savchuk-sergey/homelab_modular_tower/revisions/mk0.9.3/review_package/REVIEW_REQUIREMENTS_CHECKLIST.md

# mk0.9.3 Review Package Requirements Checklist

This checklist records whether evidence files exist. It does not approve the engineering design.

- Exports copied: `True`
- Assembly STEP present: `True`
- Analysis CSV count: `5`
- Manifest document count: `4`
- Renders included: `True`
- Drawings included: `True`

## CSV files

- `revisions/mk0.9.3/analysis/part_dimensions.csv`
- `revisions/mk0.9.3/analysis/printability_check.csv`
- `revisions/mk0.9.3/analysis/plastic_estimate.csv`
- `revisions/mk0.9.3/analysis/stl_quality.csv`
- `revisions/mk0.9.3/analysis/duplicate_geometry_check.csv`

## Manifest files

- `revisions/mk0.9.3/PRINTABLE_PARTS.md`
- `revisions/mk0.9.3/NON_PRINTABLE_PARTS.md`
- `revisions/mk0.9.3/PLACEHOLDERS.md`
- `revisions/mk0.9.3/REVIEW_GEOMETRY.md`
