savchuk-sergey/homelab_modular_tower/reviews/mk0.7.3/kimi_swarm_action_plan.md

# Action Plan for Codex — Homelab Modular Tower mk0.7.3

**Generated by:** Kimi Agents Swarm Rough Print Review  
**Date:** 2025-01-09  
**Revision:** mk0.7.3  
**Verdict:** GO FOR COUPON TEST PRINT ONLY

---

## Immediate Fixes (Before Coupon Print)

These fixes resolve BLOCKER and HIGH findings that prevent any meaningful physical assembly.

### Fix 1: Left Panel Orientation — `cad/assembly/tower_assembly.py`
**Finding:** ASM-001 (HIGH) — Left panel ribs and mounting bosses face outward.  
**Root cause:** Both left and right panels use the same `SIDE_PANEL_ASSEMBLY_ROTATION_DEG = 90.0`.  
**Fix:** Change the left panel rotation to `-90.0` (or `270.0`) so the +Y_local face (ribs/bosses) maps to +X_global, which is inward for the left panel at X=-96.5.

```python
# In tower_assembly.py, _add_side_panels():
rotations = {
    "left": -90.0,   # or 270.0
    "right": 90.0,
}
for side, (x_position, panel_factories) in factories.items():
    for index, factory in enumerate(panel_factories):
        assembly.add(
            factory(),
            name=f"{side}_side_panel_{label}",
            loc=cq.Location(
                cq.Vector(x_position, 0, side_panels.side_panel_tile_center_z(index)),
                cq.Vector(0, 0, 1),
                rotations[side],
            ),
        )
```

**Validation:** After fix, re-render `left.png` and `right.png`. Both should show smooth exteriors and ribbed interiors.

---

### Fix 2: Split-Joint Tab Overlap — `cad/parts/service_spine.py`
**Finding:** MA-003 (BLOCKER) — Both lower and upper segments have tabs at the same Z=0 location, causing physical collision.  
**Root cause:** `_split_section()` adds a tab to both lower and upper segments unconditionally.  
**Fix:** Add the tab only to the lower segment, and add a matching slot/recess to the upper segment.

```python
# In _split_section():
if section == "lower":
    tab = cq.Workplane("XY").box(...).translate((0, tab_y, tab_z))
    segment = segment.union(tab)
    segment = segment.faces(">Y").workplane(...).pushPoints(...).hole(M3_CLEARANCE)
elif section == "upper":
    # Add a matching slot/recess instead of a tab
    slot = cq.Workplane("XY").box(...).translate((0, tab_y, tab_z))
    segment = segment.cut(slot)
    # Optionally add screw holes if needed for the upper segment
```

**Validation:** After fix, run the pipeline and check that `rear_service_spine_lower` and `rear_service_spine_upper` no longer overlap in the assembly STEP export.

---

### Fix 3: Filter Retainer Clips — `cad/parts/cooling.py`
**Finding:** MA-004 (BLOCKER) — Corner clips at Y=±61 are detached from the 8 mm deep retainer body.  
**Root cause:** `clip_offset = 61` places clips 57 mm outside the body. No connecting geometry exists.  
**Fix:** Either (a) extend the retainer body depth to reach the clips, or (b) redesign the retention mechanism.

Option A (extend body):
```python
# Increase retainer depth or add ribs that connect clips to body:
connector_ribs = cq.Workplane("XY").box(BOTTOM_FILTER_RETAINER_WIDTH, clip_offset - BOTTOM_FILTER_RETAINER_DEPTH/2, BOTTOM_FILTER_RETAINER_HEIGHT)
retainer = retainer.union(connector_ribs)
```

Option B (redesign as sliding rail clips):
Replace the corner clips with small hooks that slide onto the filter frame rails.

**Validation:** After fix, the clips must be physically connected to the retainer body in the STL export. Check `stl_quality.csv` for manifold status.

---

### Fix 4: Increase Rail End Mount Engagement — `cad/parts/rails.py` or `cad/assembly/tower_assembly.py`
**Finding:** MA-002 (HIGH) — Only 3.5 mm of the 287.5 mm rail engages the mount slot.  
**Fix Option A:** Increase the slot depth in `create_rail_end_mount()`.
```python
rail_slot = cq.Workplane("XY").box(
    METAL_RAIL_WIDTH + METAL_RAIL_FRAME_CLEARANCE,
    METAL_RAIL_THICKNESS + METAL_RAIL_FRAME_CLEARANCE,
    RAIL_END_MOUNT_HEIGHT + 8.0,  # Increase from FILLET_RADIUS to +8.0
)
```

**Fix Option B:** Move the mount so the rail starts deeper in the slot.
```python
# In tower_assembly.py:
# Bottom mount: place at z = METAL_RAIL_HEIGHT/2 - (METAL_RAIL_HEIGHT - TOWER_HEIGHT + FRAME_THICKNESS) ...
# Simpler: calculate so that rail bottom enters the slot center.
```

**Validation:** After fix, the rail should engage at least 8–10 mm of the slot. Verify with a section view in the assembly.

---

### Fix 5: Add Frame Hole for Rail End Mount — `cad/parts/frame.py`
**Finding:** MA-007 (HIGH) — Rail end mount has an M3 hole with no mating target in the frame or rail.  
**Fix:** Add an M3 clearance hole to the frame at each rail position, aligned with the mount's >Y face hole.

```python
# In frame.py, after rail cutouts:
for x, y in guide_rail_positions():
    frame = frame.faces(">Z").workplane().pushPoints([(x, y)]).hole(M3_CLEARANCE)
    # Or add a dedicated mount hole offset from the rail cutout
```

**Validation:** Verify that the mount hole and frame hole are collinear in the assembly.

---

### Fix 6: Reduce Central Bottom Fan Frame Thickness — `cad/parts/feet.py` or `cad/config.py`
**Finding:** PE-001 (HIGH) — 16 mm thick, 326 g. Overbuilt for a mockup.  
**Fix:** Add a mockup parameter and reduce thickness.

```python
# In config.py, add:
MOCKUP_BASE_THICKNESS = 8.0  # mm, for rough mockup only

# In feet.py, use MOCKUP_BASE_THICKNESS instead of BASE_STABILITY_THICKNESS
# for the central_bottom_fan_frame if a mockup flag is set.
```

**Validation:** Re-export and verify the frame still has sufficient rigidity for hand-assembly.

---

## Short-Term Improvements (Before Full Mockup Print)

### Improvement 7: Add Mockup Thickness Parameters — `cad/config.py`
**Finding:** PE-002, PE-003, PE-004, PE-005 (MEDIUM) — Multiple subsystems are overbuilt for mockup.  
**Action:** Add optional `MOCKUP_*` parameters to enable quick config-driven mass reduction without altering production geometry.

```python
# In config.py:
MOCKUP_BASE_THICKNESS = 6.0
MOCKUP_CENTRAL_FRAME_THICKNESS = 8.0
MOCKUP_TRAY_BASE = 2.0
MOCKUP_TRAY_WALL = 2.0
MOCKUP_SHEAR_RIB_HEIGHT = 2.0
MOCKUP_SPINE_DEPTH = 20.0
MOCKUP_WING_THICKNESS = 6.0
```

Use these parameters in part functions when a mockup mode is enabled (e.g., via an environment variable or a config flag).

---

### Improvement 8: Generate Fastener BOM
**Finding:** RAP-007, RAP-008 (MEDIUM) — M5 nuts/washers and M3 screws/inserts are not inventoried.  
**Action:** Write a Python script that walks the assembly and counts:
- M5 nut seats (8x corner blocks × 2 faces + 4 rods × 2 ends = ~16+)
- M5 washer seats (same count)
- M3 clearance holes (panels, rails, ledges, mounts, spine, trays)
- M3 heat-set insert bosses (trays, panels, spine tabs)

Output a text file `reviews/mk0.7.3/fastener_bom.md`.

---

### Improvement 9: Write Rough Assembly Sequence
**Finding:** RAP-004 (HIGH) — No assembly instructions exist.  
**Action:** Produce a numbered step-by-step guide:

1. **Base Assembly** — Bolt together central_bottom_fan_frame, left/right extensions, front/rear wings.
2. **Rod Stack** — Insert M5 rods through bottom frame, add washers and nuts.
3. **Corner Blocks** — Slide bottom corner blocks onto rods, add washers and nuts.
4. **Guide Rails** — Insert metal guide rails into frame cutouts.
5. **Rail End Mounts** — Attach mounts at top and bottom of rails.
6. **Tray Support Ledges** — Attach ledges at module Z positions.
7. **Tray Stack** — Insert module trays from bottom to top.
8. **Rear Service Spine** — Bolt lower and upper sections together, attach to frame.
9. **Power Bus** — Attach lower and upper power bus panels, attach to spine.
10. **Side Panels** — Attach mount rails, then screw panels to rails.
11. **Fans** — Insert bottom fan cartridge, attach top/bottom grilles.
12. **Feet** — Insert TPU feet into sockets.

Include warnings about:
- Left panel orientation (must be rotated -90°)
- M5 rod cap is non-structural
- Split-joint tabs need careful alignment

---

### Improvement 10: Reduce Bottom Fan Grille Thickness — `cad/parts/cooling.py`
**Finding:** PE-009 (LOW) — Bottom grille is 7 mm thick; config specifies `FAN_GRILLE_THICKNESS=4.0`.  
**Action:** Change `bottom_fan_grille` to use `FAN_GRILLE_THICKNESS=4.0` consistently, or add a mockup parameter.

```python
# In cooling.py:
# Replace hardcoded 7 mm features with FAN_GRILLE_THICKNESS
```

---

## Validation Steps (After Fixes)

### Step 11: Re-run Revision Pipeline
After all CAD fixes, execute:
```bash
conda run -n cadquery python scripts/run_revision_pipeline.py --revision mk0.7.3
```
Verify:
- `printability_check.csv` still shows no axis-aligned overflow.
- `stl_quality.csv` still shows all printable parts as watertight/manifold.
- `plastic_estimate.csv` shows reduced mass if mockup parameters are used.

### Step 12: Print and Validate All 8 Coupons
From Section 10 of the review report:

1. **Split-joint tab coupon** — Verify tab/slot fit and M3 screw clearance.
2. **Rail end mount + metal rail coupon** — Verify 8–10 mm slot engagement and slide fit.
3. **Tray support ledge + rail + tray coupon** — Verify 1.0 mm clearance is correct after shrinkage.
4. **Side panel mount rail + panel coupon** — Verify screw fit, boss strength, and panel stiffness.
5. **Filter retainer + frame + filter coupon** — Verify clips hold filter under vibration.
6. **TPU foot + PETG socket coupon** — Verify insertion force and screw retention.
7. **Large thin flat test tile (50 × 50 × 3 mm)** — Verify brim effectiveness and corner lift.
8. **Grille test tile (50 × 50 × 4 mm section)** — Verify support-free flatness and bar adhesion.

### Step 13: Re-run This Review
After fixes and coupon validation, re-run the Kimi Agents Swarm review to confirm:
- All BLOCKERs are resolved.
- No new geometry bugs were introduced.
- The verdict can be upgraded to GO FOR ROUGH MOCKUP PRINT.

---

## Priority Summary

| Priority | Fix / Action | Effort | Impact |
|---|---|---|---|
| **P0** | Fix left panel orientation (Fix 1) | 1 line | HIGH — enables proper panel mounting |
| **P0** | Fix split-joint tab overlap (Fix 2) | ~10 lines | BLOCKER — enables spine assembly |
| **P0** | Fix filter retainer clips (Fix 3) | ~10 lines | BLOCKER — enables filter function |
| **P1** | Increase rail end mount engagement (Fix 4) | ~2 lines | HIGH — prevents rail wobble |
| **P1** | Add frame hole for rail mount (Fix 5) | ~5 lines | HIGH — gives mount a screw target |
| **P1** | Add mockup thickness parameters (Improvement 7) | ~10 lines | HIGH — saves 700–1000 g plastic |
| **P2** | Generate fastener BOM (Improvement 8) | Script | MEDIUM — enables hardware purchase |
| **P2** | Write assembly sequence (Improvement 9) | Document | HIGH — prevents misassembly |
| **P2** | Reduce central frame thickness (Fix 6) | ~3 lines | HIGH — saves ~100–130 g |
| **P3** | Reduce bottom grille thickness (Improvement 10) | ~2 lines | LOW — saves ~40 g, fixes inconsistency |

---

*End of action plan.*
