savchuk-sergey/homelab_modular_tower/reviews/mk0.7.3/kimi_swarm_unknowns.md

# Unknowns and Deferred Items — Homelab Modular Tower mk0.7.3

**Generated by:** Kimi Agents Swarm Rough Print Review  
**Date:** 2025-01-09  
**Revision:** mk0.7.3

---

## Unknowns (Insufficient Evidence in Current Review)

These items could not be fully evaluated due to missing evidence, incomplete code visibility, or the need for physical testing.

### UNK-001: Internal Component Intersections
**Status:** UNCERTAIN  
**Reference:** `cad/assembly/tower_assembly.py` (full assembly not fully dissected)  
**Question:** Do the inward-facing ribs on the right panel intersect with the Mini PC tray, rear service spine, or other internal components?  
**Why it matters:** The right panel ribs extend to X≈+85. The Mini PC tray is at X≈±86, Y≈−4 to +90. The spine is at Y≈+80. Depending on exact geometry, ribs may collide with tray edges or spine tabs.  
**What is needed:** A full assembly Boolean intersection check in CadQuery, or internal cross-section renders (e.g., X=+85 plane cut).  
**Evidence rule:** NEEDS TEST — requires CadQuery collision detection or physical test print.

### UNK-002: Mini PC Airflow Duct Internal Geometry
**Status:** UNCERTAIN  
**Reference:** `cad/parts/cooling.py` lines 137–155; `cad/assembly/tower_assembly.py`  
**Question:** Does the duct have internal baffles or overhangs that would require supports when printed upright?  
**Why it matters:** The duct is 88 × 134 × 62 mm with 2 mm walls. If it is an open U-channel, it prints support-free upright. If it has internal bridges or overhangs > 45°, supports are needed.  
**What is needed:** A small cross-section render or a test print of the duct base.  
**Evidence rule:** NEEDS TEST — requires slicer preview or physical test print.

### UNK-003: Side Panel Middle Section Printability
**Status:** UNCERTAIN  
**Reference:** `part_dimensions.csv` (`left_side_panel_middle`: 176 × 5.2 × 100.9 mm); `printability_check.csv`  
**Question:** Can the 5.2 mm thick middle panel be printed on edge (176 × 5.2 mm footprint, Z=100.9 mm) without excessive wobble or detachment?  
**Why it matters:** The middle panel is only 5.2 mm thick. Printing it on edge creates a very narrow wall on the bed. PETG may wobble or detach due to the small contact area.  
**What is needed:** A test print of the middle panel on edge with a wide brim.  
**Evidence rule:** NEEDS TEST — requires physical test print.

### UNK-004: Actual Metal Guide Rail Tolerance
**Status:** UNCERTAIN  
**Reference:** `cad/parts/rails.py`; `config.py` (`METAL_RAIL_FRAME_CLEARANCE=1.0`)  
**Question:** Is 1.0 mm clearance sufficient for real metal rail tolerance + PETG print shrinkage?  
**Why it matters:** The rail end mount slot is 11 × 4 mm for a 10 × 3 mm rail. After PETG shrinkage (~0.3–0.5 %), the slot may be too tight. If the rail has manufacturing tolerance (±0.2 mm), the fit may be too loose or too tight.  
**What is needed:** Source actual metal rails and print one rail end mount and one tray support ledge for fit testing.  
**Evidence rule:** NEEDS TEST — requires physical test with real hardware.

### UNK-005: TPU Foot Compression and Fit
**Status:** UNCERTAIN  
**Reference:** `cad/parts/feet.py`; `config.py` (`FOOT_SOCKET_CLEARANCE=0.6`, `FOOT_SCREW_DIAMETER=5.3`)  
**Question:** Will the TPU foot press-fit into the PETG socket with 0.6 mm clearance, or will it be too loose/tight?  
**Why it matters:** TPU compresses under load. 0.6 mm clearance may be too tight for insertion or too loose under the tower's weight. The 5.3 mm screw hole may not provide sufficient retention in TPU.  
**What is needed:** Print one foot socket (PETG) and one foot (TPU) and test insertion force and retention.  
**Evidence rule:** NEEDS TEST — requires physical test print.

### UNK-006: Bottom Filter Retainer Clip Strength After Print
**Status:** UNCERTAIN  
**Reference:** `cad/parts/cooling.py` lines 113–134; `stl_quality.csv`  
**Question:** Even if the clips are fixed to be geometrically attached, will they survive print removal and repeated flexing?  
**Why it matters:** The retainer clips are small (16 × 16 mm base) and only 4 mm tall. They must flex to snap over the filter frame. PETG may be too brittle for repeated snap-fit use, or the clips may break during removal from the build plate.  
**What is needed:** Print the fixed retainer and test clip retention with a real filter sheet.  
**Evidence rule:** NEEDS TEST — requires physical test print.

### UNK-007: M5 Rod Nut/Washer Stack Geometry
**Status:** UNCERTAIN  
**Reference:** `cad/parts/frame.py` lines 10–30; `cad/parts/corner_blocks.py` lines 17–20; `config.py`  
**Question:** Does the M5 nut seat + washer seat + rod end geometry allow the rod to be fully tensioned without the nut bottoming out on the frame or corner block?  
**Why it matters:** The rod extra thread allowance is 18 mm. The top frame has a nut seat (4.2 mm deep) and a washer seat (1.8 mm deep). The bottom frame has a washer seat (1.8 mm) and a nut seat (4.2 mm). The corner blocks add 28 mm height. The total stack may consume more than the 18 mm allowance if the rod is not cut to exact length.  
**What is needed:** A stack-height calculation and a physical test with actual M5 rods, nuts, and washers.  
**Evidence rule:** NEEDS TEST — requires physical assembly test.

### UNK-008: Side Panel Mount Rail Boss Strength
**Status:** UNCERTAIN  
**Reference:** `cad/parts/side_panels.py` lines 100–113; `config.py` (`INSERT_BOSS_DIAMETER=7.2`, `HEAT_SET_INSERT_M3_DIAMETER=5.2`)  
**Question:** Will the 7.2 mm diameter M3 insert boss withstand panel installation torque without stripping?  
**Why it matters:** The mount rail is 8 mm wide. The panel boss is 7.2 mm diameter. The screw must pass through the rail hole (3.4 mm) and into the panel boss insert. If the boss wall is too thin (7.2 mm OD − 5.2 mm insert = 2.0 mm wall / 2 = 1.0 mm per side), it may crack under torque.  
**What is needed:** Print one mount rail and one panel section, install a heat-set insert, and torque-test with an M3 screw.  
**Evidence rule:** NEEDS TEST — requires physical test print.

---

## Deferred to mk1.0 (Explicitly Out of Scope)

These items are intentionally deferred to the next major revision per project documentation and user instructions.

| Item | Deferred Reason | Source |
|---|---|---|
| Real Mini PC PCB/chassis dimensions, port locations, cooler height, 19 V input connector | Placeholder envelope only | `README.md` (Measurements Needed For v2); `KNOWN_ISSUES.md` |
| Real MikroTik hAP ax2 bare board dimensions, Ethernet jack position, DC input position, antenna keep-out | Placeholder envelope only | `README.md`; `KNOWN_ISSUES.md` |
| Real Raspberry Pi standoff pattern and exact connector clearance | Placeholder envelope only | `README.md` |
| DC UPS board, BMS, fuse block, terminal block, DC-DC converter footprints | Placeholder envelope only | `README.md` |
| Real connector footprints (XT30, JST-VH, Molex MicroFit, USB-C panel/cable) | Placeholder connector cutouts only | `README.md`; `KNOWN_ISSUES.md` |
| Exact LiFePO4 pack dimensions and safe retention method | Placeholder envelope only | `README.md` |
| Final Mini PC airflow duct validation against actual device intake/exhaust | Placeholder duct geometry | `KNOWN_ISSUES.md` |
| Final cable routing and wire harness engineering | Rough service envelope only | `KNOWN_ISSUES.md` |
| Thermal validation (CFD, smoke test, physical temperature measurement) | Not a mockup requirement | `KNOWN_ISSUES.md`; `REVISION.md` |
| Full production BOM and electrical safety review | mk0.7.3 is rough mockup only | `REVISION.md` |
| Final stability/tipping analysis with real component masses and CG | Rough stability envelope exists | `KNOWN_ISSUES.md`; user instruction |
| Metal guide rail material selection and stiffness validation | Non-printable reference only | `README.md` |
| Torsion brace hardware selection and physical testing | Mount provisions exist, no hardware specified | `config.py` (`TORSION_BRACE_MOUNT_ENABLED=True`) |
| Final power bus design, fuse values, DC current sizing | Placeholder power bus only | `KNOWN_ISSUES.md` |
| Final UPS/battery package and containment | Placeholder envelope only | `KNOWN_ISSUES.md` |
| Final side-panel shear-transfer architecture (mount rails are rough mockup only) | mk0.7.3 explicitly uses rough rails | `KNOWN_ISSUES.md` |
| Real SSD/SSD expansion dimensions and mounting | Placeholder envelopes only | `README.md` |
| Production cable management (cable ties, strain relief, bend radius) | Rough cable envelope only | `KNOWN_ISSUES.md` |

---

## Recommendations for Closing Unknowns

1. **Physical coupon testing is the only way to resolve UNK-001 through UNK-008.** The CSV and CAD evidence are sufficient to identify risks but insufficient to confirm fit, strength, or tolerance.
2. **After mk0.7.3 is stabilized, the mk1.0 revision should focus on:**
   - Measuring all real hardware and replacing placeholders with exact dimensions.
   - Finalizing the power bus, connector, and UPS geometry.
   - Running thermal validation (smoke test or simple temperature logging).
   - Performing a full stability analysis with measured masses.
   - Selecting and validating the metal guide rail material and dimensions.
   - Integrating the torsion brace if structural testing shows it is needed.

---

*End of unknowns and deferred items.*
