savchuk-sergey/homelab_modular_tower/reviews/mk0.7.1/agent_outputs/06_power_cable_management.md

# Power and Cable Management Review

**Reviewer:** Power and Cable Management Reviewer (Agent)  
**Revision:** mk0.7.1  
**Date:** 2026-06-27  
**Scope:** Power bus panel, power bus cover, strain relief, connector zones, rear service spine cable routing, cable exit alignment, DC UPS integration, mains isolation, fuse protection, fan cable routing.

---

## Executive Summary

The mk0.7.1 power system and cable management design is **conceptually sound** but **not physically viable** in its current state. The power bus panel and cover remain structural placeholders that will not survive real assembly. The rear service spine has insufficient cable capacity for the declared device count. Connector zones lack the clearance required for real panel-mount connectors. Strain relief is undersized. The DC UPS placeholder volume is optimistic. Most critically, there is no defined cable path for the bottom fan, and the 220 V external PSU is not physically integrated.

**The only change in mk0.7.1** is the power bus cover screw hole alignment: holes are now at `±POWER_BUS_PAD_SCREW_OFFSET_X` (±7 mm), matching the panel pad holes. This fix is correct but cosmetic; it does not address the fundamental rigidity, capacity, or routing blockers.

**Overall grade: NEEDS SIGNIFICANT REDESIGN before mk0.8.**

| Finding | Grade | Urgency |
|---|---|---|
| Power bus panel rigidity | **CONFIRMED** — inadequate | High |
| Power bus cover stiffness | **CONFIRMED** — inadequate | High |
| Strain relief sizing | **LIKELY** — too small | Medium |
| Connector zone / cover gap | **CONFIRMED** — collision | High |
| Spine cable routing capacity | **CONFIRMED** — insufficient | High |
| Cable exit alignment | **LIKELY** — too tight | Medium |
| DC UPS integration | **NEEDS TEST** | Medium |
| Mains voltage isolation | **CONFIRMED** — not modeled | Medium |
| Fuse and protection | **CONFIRMED** — placeholder only | Medium |
| Fan cable routing | **CONFIRMED** — undefined | High |

---

## Power Bus Panel Design

### Geometry
- Panel dimensions: **34 mm wide × 7.5 mm thick (max) × 275.5 mm tall** (from `config.py`: `POWER_BUS_WIDTH = 34.0`, `POWER_BUS_THICKNESS = 3.0`, `POWER_BUS_HEIGHT = 275.5`).
- Base material thickness: **3.0 mm**.
- Four rail pads: 22 mm wide × 4 mm deep × 22 mm tall, located at Z offsets `+70`, `+25`, `-20`, `-65` relative to panel center.
- M3 holes for rail pads at `±7 mm` from center, cut on the back face (`<Y`).
- No explicit mounting holes to the rear spine or frame.

### Structural Analysis
The panel is a tall, thin strip of PETG with a height-to-thickness ratio of **275.5 / 3.0 = 91.8:1**. Even with the 4 mm deep rail pads, the effective thickness is only 7.5 mm locally, and the pads are only 22 mm tall — they do not create a continuous beam. A 275 mm tall PETG panel with 3 mm base thickness will bow visibly under its own weight (estimated panel mass ≈ 30–40 g, but the real concern is cable insertion forces). When an operator plugs in an XT30 connector, the insertion force (typically 10–20 N) will flex the panel like a leaf spring. The panel has no vertical ribs, no frame tabs, and no lateral support except the cover guard rails.

The rail pads are only screwed with M3 holes, but there is no information about what they screw into. The `POWER_BUS_PAD_Y = -3.5` places the pads on the back face, but the rear spine channel wall is at Y = 65 (world), while the panel back face is at Y = 68.5. The pads do not contact the spine; they float in the channel gap.

### Evidence
- `config.py:531–533`: `POWER_BUS_THICKNESS = 3.0`, `POWER_BUS_HEIGHT = TOWER_HEIGHT - 46.0 = 275.5`.
- `service_spine.py:8–41`: The panel is a simple `box(34, 3, 275.5)` with pads and holes. No ribs, no frame mounts, no spine attachment.
- `part_dimensions.csv:83`: `power_bus_panel` bounding box is `34.0 × 7.5 × 275.5` mm.

### Grade: **CONFIRMED** — The panel is not rigid enough for real connectors.

---

## Power Bus Cover Adequacy

### Geometry
- Cover dimensions: **46 mm wide × 5.0 mm thick (max) × 265.5 mm tall** (from `config.py`: `POWER_BUS_COVER_WIDTH = 46.0`, `POWER_BUS_COVER_THICKNESS = 2.4`, `POWER_BUS_COVER_HEIGHT = 265.5`).
- Base material thickness: **2.4 mm**.
- Guard rails: 3 mm wide × 5 mm deep, running the full height on both sides.

### Structural Analysis
A 2.4 mm thick PETG panel 265 mm tall has a height-to-thickness ratio of **265.5 / 2.4 = 110.6:1**. This is even more flexible than the panel. The guard rails add some stiffness, but they are only 3 mm wide and 5 mm deep — they act as edge stiffeners, not as structural ribs. The cover will act as a leaf spring. During assembly or when cables are pressed against it, it will bow inward toward the panel. With only ~0.2 mm gap between the cover guard rails and the panel back face, even slight deflection will cause contact and potential shorting if wires are routed in the gap.

The cover is now mounted with M3 screws at the correct `±7 mm` X offsets, matching the panel rail pads. The code uses `for _, z in cfg.POWER_BUS_RAIL_LABELS: cover.hole(M3_CLEARANCE)` at the rail Z positions, with holes at `(-7, z)` and `(7, z)`. This means there are still only **4 screw pairs** (8 holes) along the entire 265 mm height, spaced at rail positions (70, 25, -20, -65). For a 265 mm tall cover, 4 screw pairs are insufficient to prevent bowing between screws. The span between screws is ~45–90 mm, and a 2.4 mm PETG panel will sag between mounts.

### Fix Verification
The mk0.7.1 change in `service_spine.py:57–60` correctly sets the cover holes to `±POWER_BUS_PAD_SCREW_OFFSET_X` (7.0 mm), matching the panel M3 holes. This is a valid bug fix, but it does not change the structural assessment.

### Evidence
- `config.py:551–554`: `POWER_BUS_COVER_THICKNESS = 2.4`, `POWER_BUS_COVER_HEIGHT = 265.5`.
- `service_spine.py:44–61`: Cover is a `box(46, 2.4, 265.5)` with guard rails and 8 M3 holes at ±7 mm.
- `part_dimensions.csv:82`: `power_bus_cover` bounding box is `46.0 × 5.0 × 265.5` mm.

### Grade: **CONFIRMED** — The cover will flex significantly and is insufficiently supported. The hole alignment fix is correct but insufficient for structural viability.

---

## Strain Relief Analysis

### Geometry
- Strain relief clamps: **24 mm wide × 8 mm tall × 6 mm deep** (`POWER_BUS_STRAIN_RELIEF_WIDTH = 24.0`, `POWER_BUS_STRAIN_RELIEF_HEIGHT = 8.0`, `POWER_BUS_STRAIN_RELIEF_DEPTH = 6.0`).
- Four clamps at Z positions: `-112`, `-48`, `+48`, `+112` relative to panel center.
- Each clamp has a cable tie slot: `slot2D(12, 4, 0)` — i.e., **4 mm wide × 12 mm tall** slot.

### Analysis
An XT30 connector with 14 AWG silicone wire has a wire bundle diameter of approximately **4.5–5.5 mm**. The clamp height is only **8 mm**, which means the clamp can barely accommodate one cable in the vertical direction. The clamp depth is **6 mm**, which is the thickness of the clamp body in the Y direction. The cable tie slot is only **4 mm wide** — standard cable ties are 2.5–4.8 mm wide, so this just fits a small tie, but the slot is cut through the entire clamp, meaning the cable is only constrained by the cable tie, not by a proper saddle or gland.

For USB-C cables with thicker molded strain relief (6–8 mm diameter), the clamp is too small entirely. For Ethernet cables (Cat 6, ~6 mm diameter), the clamp is also undersized. The clamps are essentially small PETG blocks with a through-slot — they provide no clamping force without a cable tie, and the cable tie slot is too small to use a proper locking tie.

Furthermore, the clamps are placed only at the four connector zone heights. If a module uses a cable that is longer or routed differently, there is no intermediate strain relief.

### Evidence
- `config.py:556–559`: Strain relief dimensions and Z positions.
- `service_spine.py:29–40`: Clamp geometry and cable tie slot.
- Render image: The clamps are small protrusions on the panel sides.

### Grade: **LIKELY** — Strain relief is inadequate for typical XT30 and USB-C cables with thick insulation.

---

## Connector Zone Sizing

### Geometry
Connector zones are through-cut rectangular cutouts on the panel back face (`<Y`):

| Zone | Dimensions (W×H) | Z Position (rel. center) | Rail | Rail Z (rel. center) |
|---|---|---|---|---|
| XT30 (19V) | 24 × 14 mm | +112 mm | 19V | +70 mm |
| MicroFit (12V) | 20 × 10 mm | +48 mm | 12V | +25 mm |
| USB-C (5V) | 18 × 8 mm | -48 mm | 5V | -20 mm |
| Cable tie | 24 × 10 mm | -112 mm | GND | -65 mm |

### Critical Gap Problem
The connector zones are cut through the 3.0 mm panel with `cutBlind(-5.0)`, making them through-holes. The connectors would be mounted on the panel front face (`>Y`, Y = 71.5 world). However, the **cover is only 2.2–3.2 mm behind the panel back face** (Y = 68.5 for panel back, Y = 65.8–68.3 for cover assembly). This leaves **0.2–2.7 mm** of clearance behind the panel.

A panel-mount XT30 connector has a body that extends **10–15 mm** behind the mounting flange. A MicroFit panel mount extends **8–12 mm** behind. A USB-C panel mount extends **6–10 mm**. All of these would **collide with the cover or guard rails**.

### Vertical Alignment Problem
The connector zones are not aligned with the rail pads. For example, the XT30 zone is at Z = +112 mm, but the 19V rail pad is at Z = +70 mm. The vertical offset is 42 mm. This means the connector is 42 mm away from the rail it serves. The wires would need to run internally 42 mm, but the panel is only 3 mm thick — there is no internal wiring channel. The actual wiring would need to snake around the panel edges, which are only 5 mm from the panel side (panel is 34 mm wide, rail pads are 22 mm wide, leaving 6 mm margins).

### Horizontal Alignment Problem
The module cable exits are 66 mm wide, but the power bus panel is only 34 mm wide. The connector zones are centered at X = 0. However, some devices have their power jacks offset:
- Mini PC power window is at `X = -54.0` relative to tray center (`config.py:306`).
- The power bus panel is at X = 0 world, so the Mini PC power connector at X = -54 would need to reach 54 mm horizontally to the centered connector zone. But the power bus panel is only 17 mm wide from center to edge (34 mm total). The connector at X = -54 is outside the panel entirely.
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
