savchuk-sergey/homelab_modular_tower/revisions/mk0.9.3/NON_PRINTABLE_PARTS.md

# Non-Printable Reference Parts

Revision: `mk0.9.3`

This manifest lists generated export artifacts. CadQuery source remains the source of truth.

No artifacts found for this category.
