savchuk-sergey/homelab_modular_tower/revisions/mk0.9.1/BOM.md

# mk0.9.1 Bill of Materials (BOM)

## Printed parts (PETG)

| Part | Target weight | Qty | Notes |
|---|---|-----|---|
| Base module | 180–260 g | 1 | Frame + fan mount + grill + filter slot + foot mounts |
| RPi/SSD carriage | 80–130 g | 1 | Open-frame, 4 POM-C shoes |
| Mini PC placeholder carriage | 100–180 g | 1 | Open-frame, 6 POM-C shoes |
| Roof module | 150–230 g | 1 | Frame + fan mount + grill + shroud |
| M5 rod caps | 5–10 g | 4 | Protective end caps |
| Rail end clips | 2–4 g | 4 | Retain U-channel rail ends |
| Small brackets / stops | 10–20 g | — | Miscellaneous |
| **Total PETG target** | **750–900 g** | | |
| **Total PETG hard limit** | **≤ 1100 g** | | |

## Printed parts (TPU)

| Part | Target weight | Qty | Notes |
|---|---|-----|---|
| TPU feet | 8–12 g | 4 | Replaceable, M5 through-hole |
| **Total TPU target** | **≤ 50 g** | | |

## Hardware

| Item | Qty | Notes |
|---|-----|---|
| M5 threaded rod × 4 | 4 | Length = tower height + ~18 mm thread allowance |
| M5 nut | 8 | 4 bottom, 4 top |
| M5 washer | 8 | Optional, spreads load on frame |
| M3 × 12 mm screw | ~20 | Module interfaces, rail clips, shoe clamps |
| M3 × 16 mm screw | 4 | Front carriage locks |
| M3 heat-set insert | ~20 | Brass, ~5 mm OD, 4 mm length |
| M3 × 4 mm screw | 8 | 120 mm fan mounting (4 per fan) |

## Commercial / non-printed parts

| Item | Qty | Notes |
|---|-----|---|
| Aluminum U-channel 15 × 10 × 10 × 2 mm | 2 × 145 mm + 2 × 155 mm | Side rails for carriages; cut from 1800 mm stock |
| POM-C rod Ø8 mm | 1 × 500 mm | Cut into 12 mm shoe blanks (4 + 6 + spares) |
| 120 mm × 120 mm × 25 mm fan | 2 | Bottom intake, top exhaust |
| Dust filter material | 1 sheet | Cut to fit filter slot |
| Top guard mesh | 1 sheet | Optional coarse filter for exhaust |

## Electronics (placeholder)

| Item | Qty | Notes |
|---|-----|---|
| Raspberry Pi 3B | 1 | Mounted on carriage standoffs |
| External SSD | 1 | 2.5" or M.2 enclosure |
| Mini PC placeholder | 1 | Real device measured in mk1.0 |
