savchuk-sergey/homelab_modular_tower/revisions/mk0.9.2/NON_PRINTABLE_PARTS.md

# Non-Printable Reference Parts

Revision: `mk0.9.2`

This manifest lists generated export artifacts. CadQuery source remains the source of truth.

## aluminum_u_channel_rail_placeholder

- Category: `non_printable`
- STEP: `exports/mk0.9.2/non_printable/metal_reference/aluminum_u_channel_rail_placeholder.step`
- STL: `exports/mk0.9.2/non_printable/metal_reference/aluminum_u_channel_rail_placeholder.stl`

## m5_threaded_rod

- Category: `non_printable`
- STEP: `exports/mk0.9.2/non_printable/metal_reference/m5_threaded_rod.step`
- STL: `exports/mk0.9.2/non_printable/metal_reference/m5_threaded_rod.stl`
