savchuk-sergey/homelab_modular_tower/revisions/mk0.9.2/PRINTABLE_PARTS.md

# Printable Parts

Revision: `mk0.9.2`

This manifest lists generated export artifacts. CadQuery source remains the source of truth.

## base_module

- Category: `printable`
- STEP: `exports/mk0.9.2/printable/plastic/base_module.step`
- STL: `exports/mk0.9.2/printable/plastic/base_module.stl`

## bottom_grill

- Category: `printable`
- STEP: `exports/mk0.9.2/printable/plastic/bottom_grill.step`
- STL: `exports/mk0.9.2/printable/plastic/bottom_grill.stl`

## dust_filter_slot

- Category: `printable`
- STEP: `exports/mk0.9.2/printable/plastic/dust_filter_slot.step`
- STL: `exports/mk0.9.2/printable/plastic/dust_filter_slot.stl`

## foot_mounts

- Category: `printable`
- STEP: `exports/mk0.9.2/printable/plastic/foot_mounts.step`
- STL: `exports/mk0.9.2/printable/plastic/foot_mounts.stl`

## m5_threaded_rod_cap

- Category: `printable`
- STEP: `exports/mk0.9.2/printable/plastic/m5_threaded_rod_cap.step`
- STL: `exports/mk0.9.2/printable/plastic/m5_threaded_rod_cap.stl`

## mini_pc_placeholder_carriage

- Category: `printable`
- STEP: `exports/mk0.9.2/printable/plastic/mini_pc_placeholder_carriage.step`
- STL: `exports/mk0.9.2/printable/plastic/mini_pc_placeholder_carriage.stl`

## mini_pc_placeholder_module

- Category: `printable`
- STEP: `exports/mk0.9.2/printable/plastic/mini_pc_placeholder_module.step`
- STL: `exports/mk0.9.2/printable/plastic/mini_pc_placeholder_module.stl`

## rail_end_clip

- Category: `printable`
- STEP: `exports/mk0.9.2/printable/plastic/rail_end_clip.step`
- STL: `exports/mk0.9.2/printable/plastic/rail_end_clip.stl`

## roof_module

- Category: `printable`
- STEP: `exports/mk0.9.2/printable/plastic/roof_module.step`
- STL: `exports/mk0.9.2/printable/plastic/roof_module.stl`

## rpi_ssd_carriage

- Category: `printable`
- STEP: `exports/mk0.9.2/printable/plastic/rpi_ssd_carriage.step`
- STL: `exports/mk0.9.2/printable/plastic/rpi_ssd_carriage.stl`

## rpi_ssd_module

- Category: `printable`
- STEP: `exports/mk0.9.2/printable/plastic/rpi_ssd_module.step`
- STL: `exports/mk0.9.2/printable/plastic/rpi_ssd_module.stl`

## top_filter_slot

- Category: `printable`
- STEP: `exports/mk0.9.2/printable/plastic/top_filter_slot.step`
- STL: `exports/mk0.9.2/printable/plastic/top_filter_slot.stl`

## foot

- Category: `printable`
- STEP: `exports/mk0.9.2/printable/tpu/foot.step`
- STL: `exports/mk0.9.2/printable/tpu/foot.stl`

## tpu_foot_placeholder

- Category: `printable`
- STEP: `exports/mk0.9.2/printable/tpu/tpu_foot_placeholder.step`
- STL: `exports/mk0.9.2/printable/tpu/tpu_foot_placeholder.stl`
