savchuk-sergey/homelab_modular_tower/revisions/mk0.7.3/PRINTABLE_PARTS.md

# Printable Parts

Revision: `mk0.7.3`

This manifest lists generated export artifacts. CadQuery source remains the source of truth.

## bottom_fan_cartridge

- Category: `printable`
- STEP: `exports/mk0.7.3/printable/plastic/bottom_fan_cartridge.step`
- STL: `exports/mk0.7.3/printable/plastic/bottom_fan_cartridge.stl`

## bottom_fan_grille

- Category: `printable`
- STEP: `exports/mk0.7.3/printable/plastic/bottom_fan_grille.step`
- STL: `exports/mk0.7.3/printable/plastic/bottom_fan_grille.stl`

## bottom_filter_frame

- Category: `printable`
- STEP: `exports/mk0.7.3/printable/plastic/bottom_filter_frame.step`
- STL: `exports/mk0.7.3/printable/plastic/bottom_filter_frame.stl`

## bottom_filter_retainer

- Category: `printable`
- STEP: `exports/mk0.7.3/printable/plastic/bottom_filter_retainer.step`
- STL: `exports/mk0.7.3/printable/plastic/bottom_filter_retainer.stl`

## bottom_structural_frame

- Category: `printable`
- STEP: `exports/mk0.7.3/printable/plastic/bottom_structural_frame.step`
- STL: `exports/mk0.7.3/printable/plastic/bottom_structural_frame.stl`

## central_bottom_fan_frame

- Category: `printable`
- STEP: `exports/mk0.7.3/printable/plastic/central_bottom_fan_frame.step`
- STL: `exports/mk0.7.3/printable/plastic/central_bottom_fan_frame.stl`

## corner_block

- Category: `printable`
- STEP: `exports/mk0.7.3/printable/plastic/corner_block.step`
- STL: `exports/mk0.7.3/printable/plastic/corner_block.stl`

## external_ssd_bay

- Category: `printable`
- STEP: `exports/mk0.7.3/printable/plastic/external_ssd_bay.step`
- STL: `exports/mk0.7.3/printable/plastic/external_ssd_bay.stl`

## foot_socket

- Category: `printable`
- STEP: `exports/mk0.7.3/printable/plastic/foot_socket.step`
- STL: `exports/mk0.7.3/printable/plastic/foot_socket.stl`

## front_stability_wing

- Category: `printable`
- STEP: `exports/mk0.7.3/printable/plastic/front_stability_wing.step`
- STL: `exports/mk0.7.3/printable/plastic/front_stability_wing.stl`

## left_foot_extension

- Category: `printable`
- STEP: `exports/mk0.7.3/printable/plastic/left_foot_extension.step`
- STL: `exports/mk0.7.3/printable/plastic/left_foot_extension.stl`

## left_side_panel_lower

- Category: `printable`
- STEP: `exports/mk0.7.3/printable/plastic/left_side_panel_lower.step`
- STL: `exports/mk0.7.3/printable/plastic/left_side_panel_lower.stl`

## left_side_panel_middle

- Category: `printable`
- STEP: `exports/mk0.7.3/printable/plastic/left_side_panel_middle.step`
- STL: `exports/mk0.7.3/printable/plastic/left_side_panel_middle.stl`

## left_side_panel_upper

- Category: `printable`
- STEP: `exports/mk0.7.3/printable/plastic/left_side_panel_upper.step`
- STL: `exports/mk0.7.3/printable/plastic/left_side_panel_upper.stl`

## m5_threaded_rod_cap

- Category: `printable`
- STEP: `exports/mk0.7.3/printable/plastic/m5_threaded_rod_cap.step`
- STL: `exports/mk0.7.3/printable/plastic/m5_threaded_rod_cap.stl`

## mikrotik_tray

- Category: `printable`
- STEP: `exports/mk0.7.3/printable/plastic/mikrotik_tray.step`
- STL: `exports/mk0.7.3/printable/plastic/mikrotik_tray.stl`

## mini_pc_airflow_duct

- Category: `printable`
- STEP: `exports/mk0.7.3/printable/plastic/mini_pc_airflow_duct.step`
- STL: `exports/mk0.7.3/printable/plastic/mini_pc_airflow_duct.stl`

## mini_pc_tray

- Category: `printable`
- STEP: `exports/mk0.7.3/printable/plastic/mini_pc_tray.step`
- STL: `exports/mk0.7.3/printable/plastic/mini_pc_tray.stl`

## mini_pc_tray_stop

- Category: `printable`
- STEP: `exports/mk0.7.3/printable/plastic/mini_pc_tray_stop.step`
- STL: `exports/mk0.7.3/printable/plastic/mini_pc_tray_stop.stl`

## power_bus_cover_lower

- Category: `printable`
- STEP: `exports/mk0.7.3/printable/plastic/power_bus_cover_lower.step`
- STL: `exports/mk0.7.3/printable/plastic/power_bus_cover_lower.stl`

## power_bus_cover_upper

- Category: `printable`
- STEP: `exports/mk0.7.3/printable/plastic/power_bus_cover_upper.step`
- STL: `exports/mk0.7.3/printable/plastic/power_bus_cover_upper.stl`

## power_bus_panel_lower

- Category: `printable`
- STEP: `exports/mk0.7.3/printable/plastic/power_bus_panel_lower.step`
- STL: `exports/mk0.7.3/printable/plastic/power_bus_panel_lower.stl`

## power_bus_panel_upper

- Category: `printable`
- STEP: `exports/mk0.7.3/printable/plastic/power_bus_panel_upper.step`
- STL: `exports/mk0.7.3/printable/plastic/power_bus_panel_upper.stl`

## rail_end_mount

- Category: `printable`
- STEP: `exports/mk0.7.3/printable/plastic/rail_end_mount.step`
- STL: `exports/mk0.7.3/printable/plastic/rail_end_mount.stl`

## raspberry_pi_tray

- Category: `printable`
- STEP: `exports/mk0.7.3/printable/plastic/raspberry_pi_tray.step`
- STL: `exports/mk0.7.3/printable/plastic/raspberry_pi_tray.stl`

## rear_service_spine_cover_lower

- Category: `printable`
- STEP: `exports/mk0.7.3/printable/plastic/rear_service_spine_cover_lower.step`
- STL: `exports/mk0.7.3/printable/plastic/rear_service_spine_cover_lower.stl`

## rear_service_spine_cover_upper

- Category: `printable`
- STEP: `exports/mk0.7.3/printable/plastic/rear_service_spine_cover_upper.step`
- STL: `exports/mk0.7.3/printable/plastic/rear_service_spine_cover_upper.stl`

## rear_service_spine_lower

- Category: `printable`
- STEP: `exports/mk0.7.3/printable/plastic/rear_service_spine_lower.step`
- STL: `exports/mk0.7.3/printable/plastic/rear_service_spine_lower.stl`

## rear_service_spine_upper

- Category: `printable`
- STEP: `exports/mk0.7.3/printable/plastic/rear_service_spine_upper.step`
- STL: `exports/mk0.7.3/printable/plastic/rear_service_spine_upper.stl`

## rear_stability_wing

- Category: `printable`
- STEP: `exports/mk0.7.3/printable/plastic/rear_stability_wing.step`
- STL: `exports/mk0.7.3/printable/plastic/rear_stability_wing.stl`

## right_foot_extension

- Category: `printable`
- STEP: `exports/mk0.7.3/printable/plastic/right_foot_extension.step`
- STL: `exports/mk0.7.3/printable/plastic/right_foot_extension.stl`

## right_side_panel_lower

- Category: `printable`
- STEP: `exports/mk0.7.3/printable/plastic/right_side_panel_lower.step`
- STL: `exports/mk0.7.3/printable/plastic/right_side_panel_lower.stl`

## right_side_panel_middle

- Category: `printable`
- STEP: `exports/mk0.7.3/printable/plastic/right_side_panel_middle.step`
- STL: `exports/mk0.7.3/printable/plastic/right_side_panel_middle.stl`

## right_side_panel_upper

- Category: `printable`
- STEP: `exports/mk0.7.3/printable/plastic/right_side_panel_upper.step`
- STL: `exports/mk0.7.3/printable/plastic/right_side_panel_upper.stl`

## side_panel_mount_rail_lower

- Category: `printable`
- STEP: `exports/mk0.7.3/printable/plastic/side_panel_mount_rail_lower.step`
- STL: `exports/mk0.7.3/printable/plastic/side_panel_mount_rail_lower.stl`

## side_panel_mount_rail_middle

- Category: `printable`
- STEP: `exports/mk0.7.3/printable/plastic/side_panel_mount_rail_middle.step`
- STL: `exports/mk0.7.3/printable/plastic/side_panel_mount_rail_middle.stl`

## side_panel_mount_rail_upper

- Category: `printable`
- STEP: `exports/mk0.7.3/printable/plastic/side_panel_mount_rail_upper.step`
- STL: `exports/mk0.7.3/printable/plastic/side_panel_mount_rail_upper.stl`

## ssd_expansion_tray

- Category: `printable`
- STEP: `exports/mk0.7.3/printable/plastic/ssd_expansion_tray.step`
- STL: `exports/mk0.7.3/printable/plastic/ssd_expansion_tray.stl`

## top_fan_grille

- Category: `printable`
- STEP: `exports/mk0.7.3/printable/plastic/top_fan_grille.step`
- STL: `exports/mk0.7.3/printable/plastic/top_fan_grille.stl`

## top_structural_frame

- Category: `printable`
- STEP: `exports/mk0.7.3/printable/plastic/top_structural_frame.step`
- STL: `exports/mk0.7.3/printable/plastic/top_structural_frame.stl`

## tray_support_ledge

- Category: `printable`
- STEP: `exports/mk0.7.3/printable/plastic/tray_support_ledge.step`
- STL: `exports/mk0.7.3/printable/plastic/tray_support_ledge.stl`

## ups_power_tray

- Category: `printable`
- STEP: `exports/mk0.7.3/printable/plastic/ups_power_tray.step`
- STL: `exports/mk0.7.3/printable/plastic/ups_power_tray.stl`

## foot

- Category: `printable`
- STEP: `exports/mk0.7.3/printable/tpu/foot.step`
- STL: `exports/mk0.7.3/printable/tpu/foot.stl`
