savchuk-sergey/homelab_modular_tower/revisions/mk0.7/review_package/manifests/NON_PRINTABLE_PARTS.md

# Non-Printable Reference Parts

Revision: `mk0.7`

This manifest lists generated export artifacts. CadQuery source remains the source of truth.

## m5_threaded_rod

- Category: `non_printable`
- STEP: `exports/mk0.7/non_printable/metal_reference/m5_threaded_rod.step`
- STL: `exports/mk0.7/non_printable/metal_reference/m5_threaded_rod.stl`

## metal_guide_rail

- Category: `non_printable`
- STEP: `exports/mk0.7/non_printable/metal_reference/metal_guide_rail.step`
- STL: `exports/mk0.7/non_printable/metal_reference/metal_guide_rail.stl`
