savchuk-sergey/homelab_modular_tower/revisions/mk0.7/review_package/exports/review/airflow_path_review.step

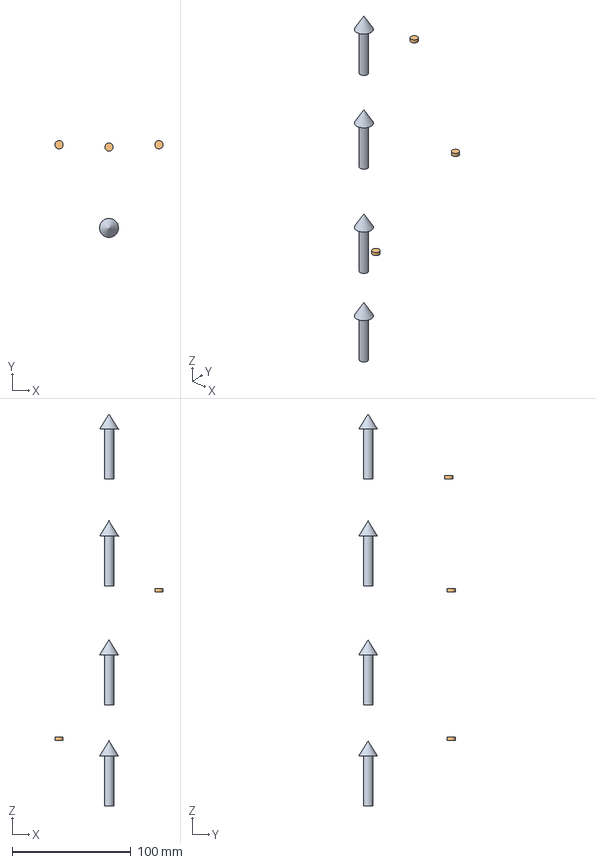
[picture p15: CAD file, 2026-06-27, last stored version]
revisions/mk0.7/review_package/exports/review/airflow_path_review.step
91.0 x 81.5 x 329.8 mm
