savchuk-sergey/homelab_modular_tower/revisions/mk0.7/review_package/exports/placeholders/devices/ssd_expansion_placeholder.step

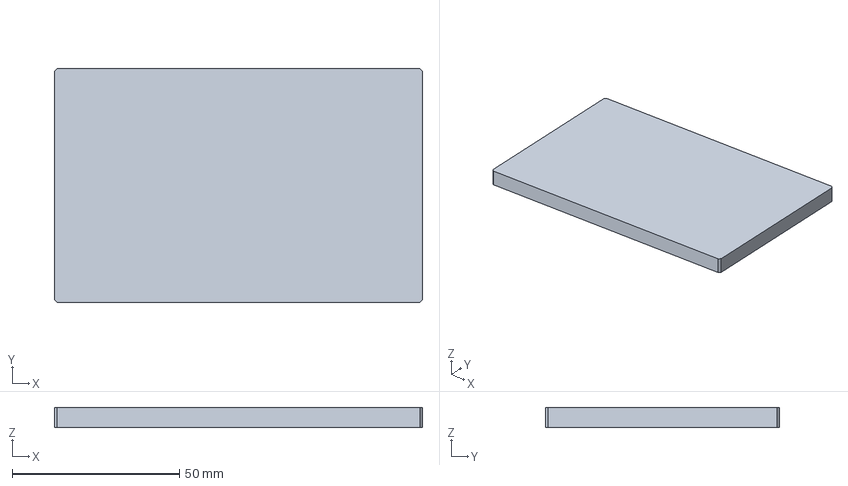
[picture p16: CAD file, 2026-06-27, last stored version]
revisions/mk0.7/review_package/exports/placeholders/devices/ssd_expansion_placeholder.step
110.0 x 70.0 x 6.00 mm
