savchuk-sergey/homelab_modular_tower/revisions/mk0.7/review_package/exports/review/printability_layout_review.step

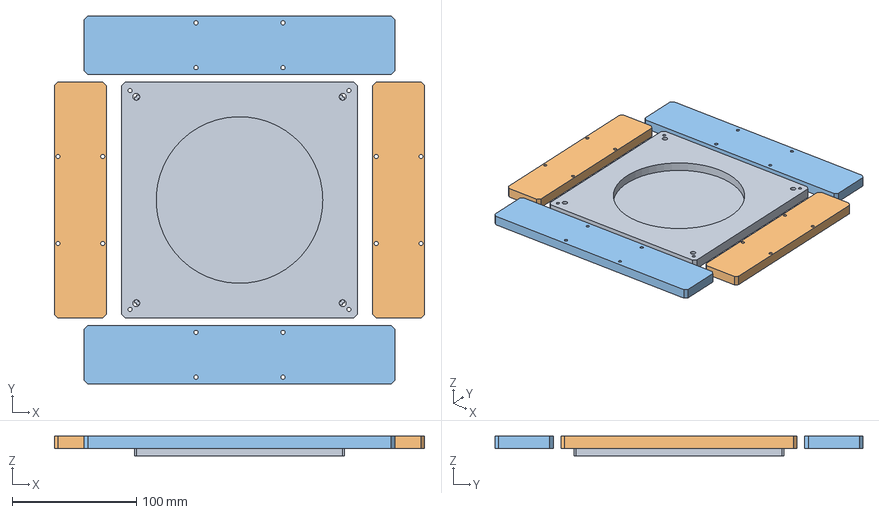
[picture p18: CAD file, 2026-06-27, last stored version]
revisions/mk0.7/review_package/exports/review/printability_layout_review.step
298.0 x 296.0 x 16.0 mm
