savchuk-sergey/homelab_modular_tower/revisions/mk0.7/review_package/exports/placeholders/devices/ssd_placeholder.step

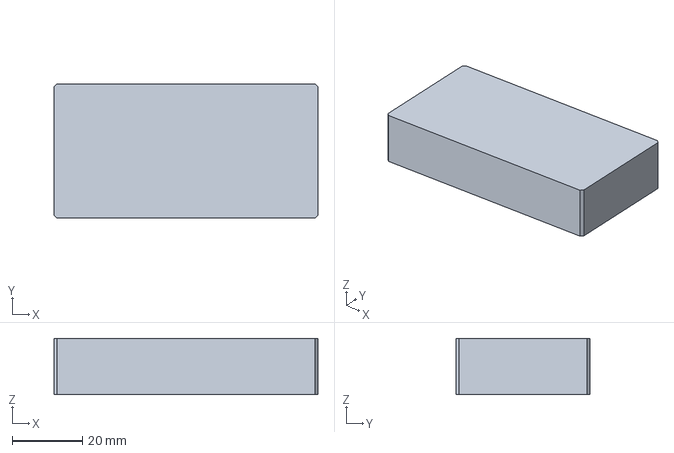
[picture p19: CAD file, 2026-06-27, last stored version]
revisions/mk0.7/review_package/exports/placeholders/devices/ssd_placeholder.step
75.0 x 38.0 x 16.0 mm
