savchuk-sergey/homelab_modular_tower/revisions/mk0.7/review_package/exports/printable/plastic/central_bottom_fan_frame.step

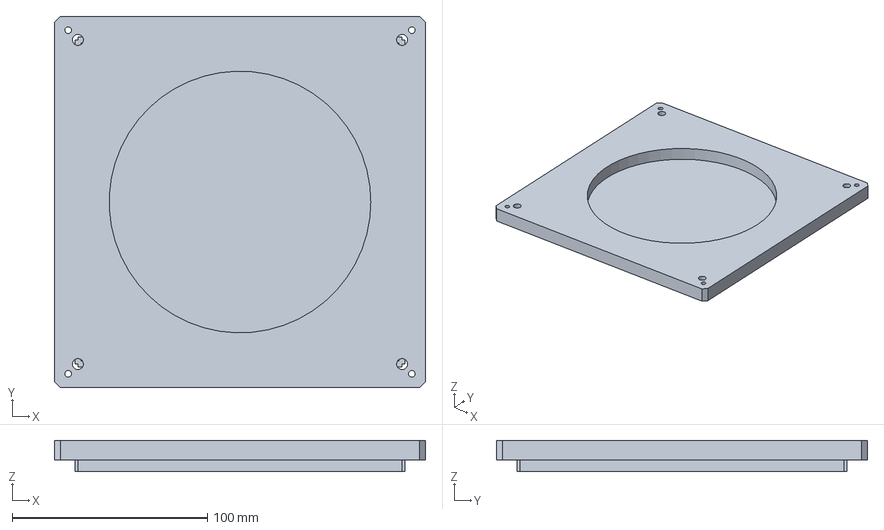
[picture p20: CAD file, 2026-06-27, last stored version]
revisions/mk0.7/review_package/exports/printable/plastic/central_bottom_fan_frame.step
190.0 x 190.0 x 16.0 mm
