savchuk-sergey/homelab_modular_tower/revisions/mk0.7/review_package/exports/review/bottom_intake_open_area_review.step

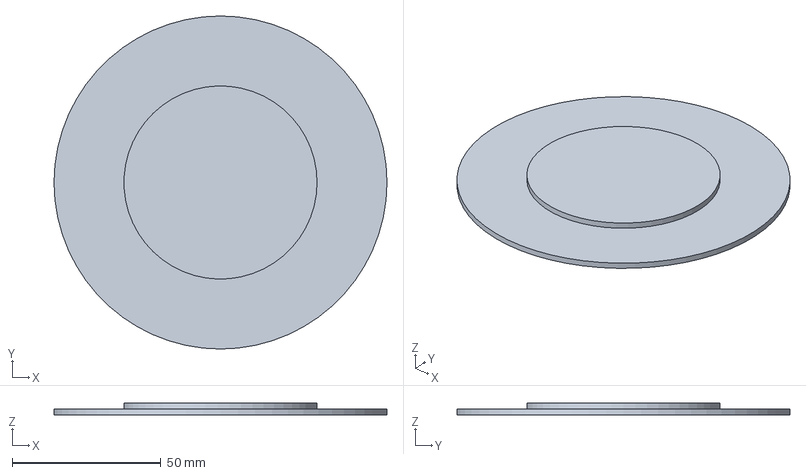
[picture p21: CAD file, 2026-06-27, last stored version]
revisions/mk0.7/review_package/exports/review/bottom_intake_open_area_review.step
112.0 x 112.0 x 4.00 mm
