savchuk-sergey/homelab_modular_tower/exports/mk0.1/step/top_fan_panel.step

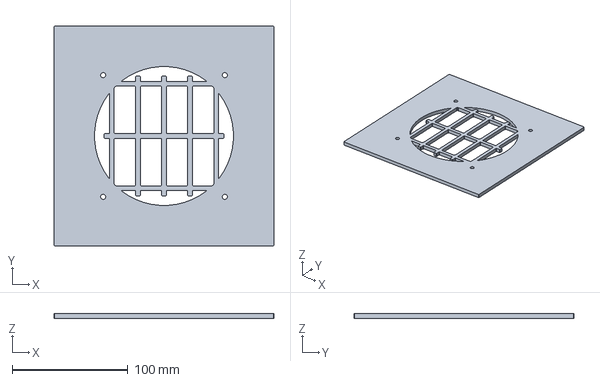
[picture p22: CAD file, 2026-06-27, last stored version]
exports/mk0.1/step/top_fan_panel.step
190.0 x 190.0 x 4.00 mm
