savchuk-sergey/homelab_modular_tower/revisions/mk0.7/review_package/exports/printable/plastic/bottom_filter_frame.step

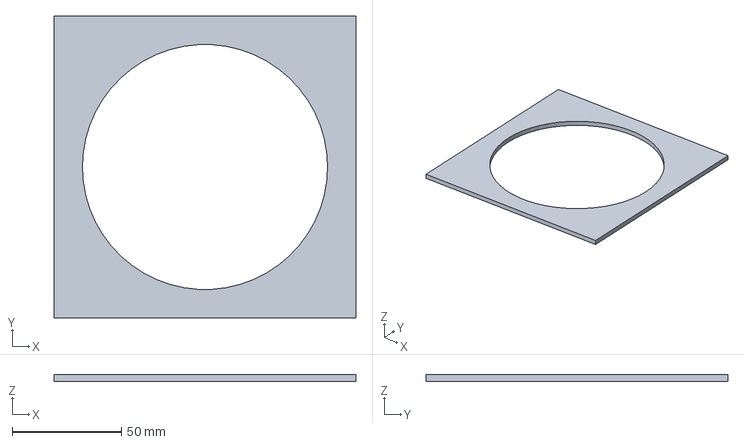
[picture p24: CAD file, 2026-06-27, last stored version]
revisions/mk0.7/review_package/exports/printable/plastic/bottom_filter_frame.step
138.0 x 138.0 x 3.00 mm
