savchuk-sergey/homelab_modular_tower/exports/mk0.1/step/left_side_panel.step

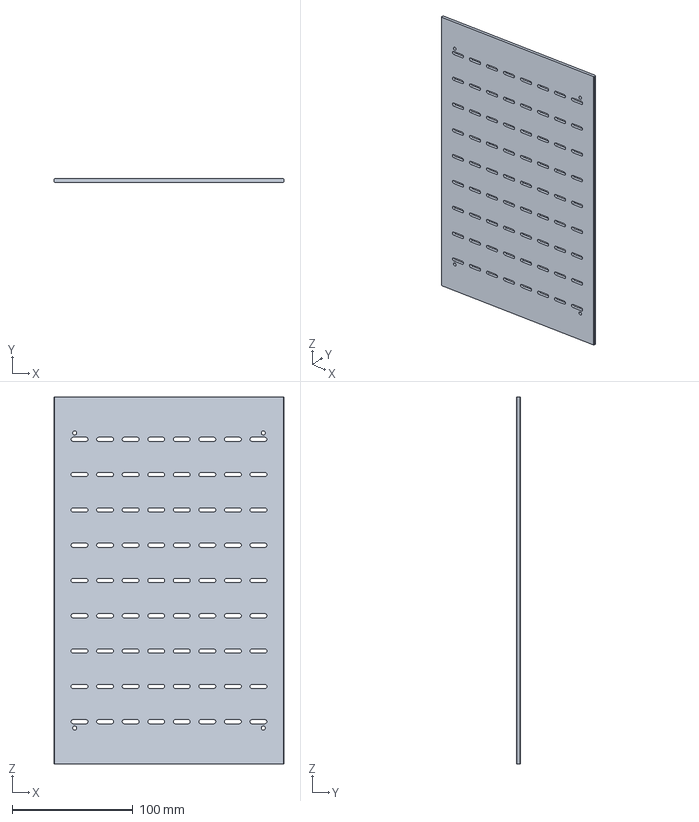
[picture p25: CAD file, 2026-06-27, last stored version]
exports/mk0.1/step/left_side_panel.step
190.0 x 3.00 x 303.5 mm
