savchuk-sergey/homelab_modular_tower/revisions/mk0.7/review_package/exports/printable/plastic/corner_block.step

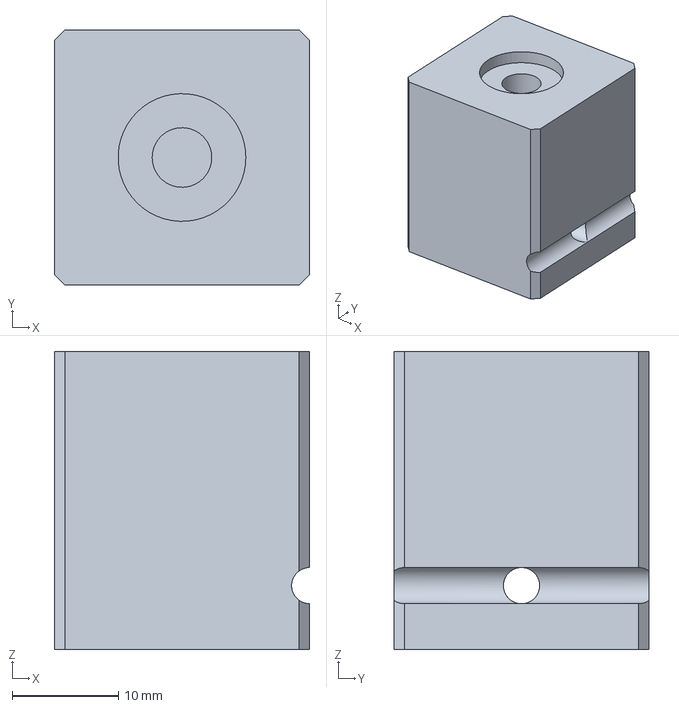
[picture p26: CAD file, 2026-06-27, last stored version]
revisions/mk0.7/review_package/exports/printable/plastic/corner_block.step
24.0 x 24.0 x 28.0 mm
