savchuk-sergey/homelab_modular_tower/revisions/mk0.7/review_package/exports/printable/plastic/front_stability_wing.step

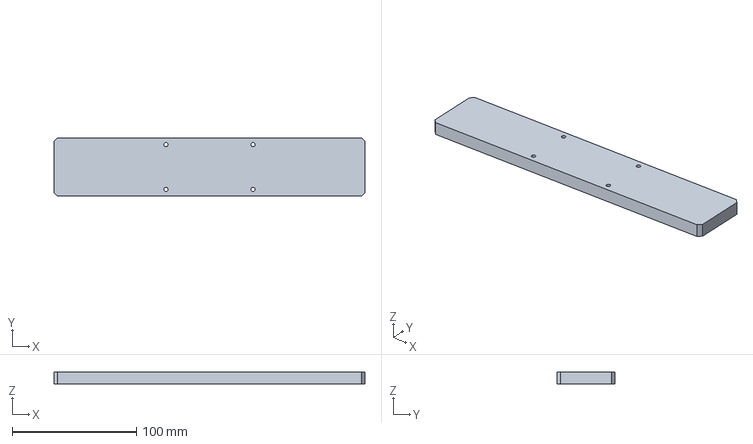
[picture p27: CAD file, 2026-06-27, last stored version]
revisions/mk0.7/review_package/exports/printable/plastic/front_stability_wing.step
250.0 x 47.0 x 10.0 mm
