savchuk-sergey/homelab_modular_tower/exports/mk0.1/step/m5_threaded_rod.step

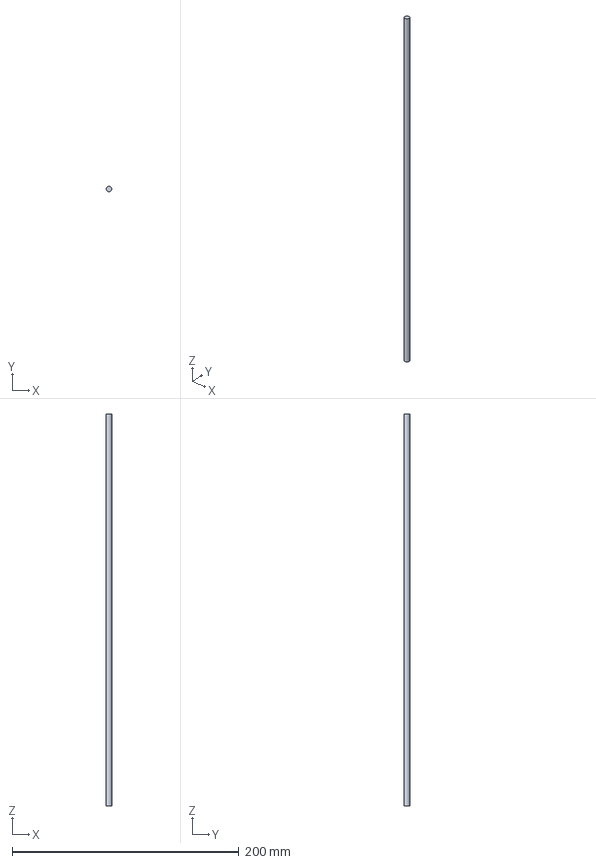
[picture p29: CAD file, 2026-06-27, last stored version]
exports/mk0.1/step/m5_threaded_rod.step
5.00 x 5.00 x 345.5 mm
