savchuk-sergey/homelab_modular_tower/revisions/mk0.7/review_package/exports/printable/plastic/foot_socket.step

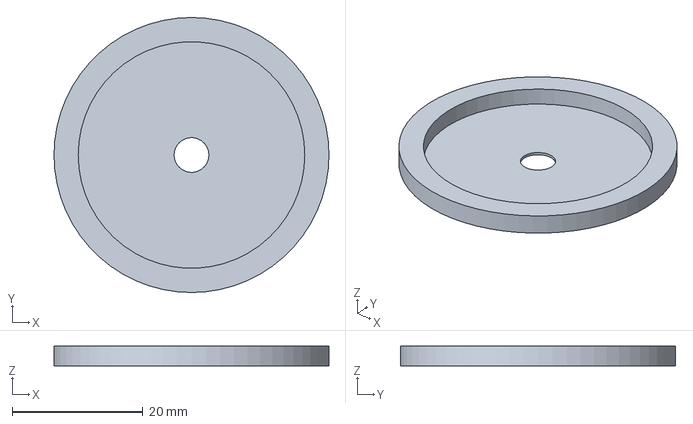
[picture p30: CAD file, 2026-06-27, last stored version]
revisions/mk0.7/review_package/exports/printable/plastic/foot_socket.step
42.0 x 42.0 x 3.00 mm
