savchuk-sergey/homelab_modular_tower/exports/mk0.1/step/bottom_fan_panel.step

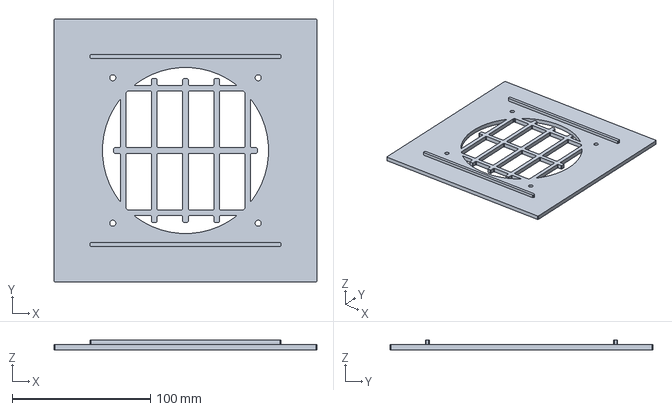
[picture p31: CAD file, 2026-06-27, last stored version]
exports/mk0.1/step/bottom_fan_panel.step
190.0 x 190.0 x 7.00 mm
