savchuk-sergey/homelab_modular_tower/revisions/mk0.7/review_package/exports/printable/plastic/external_ssd_bay.step

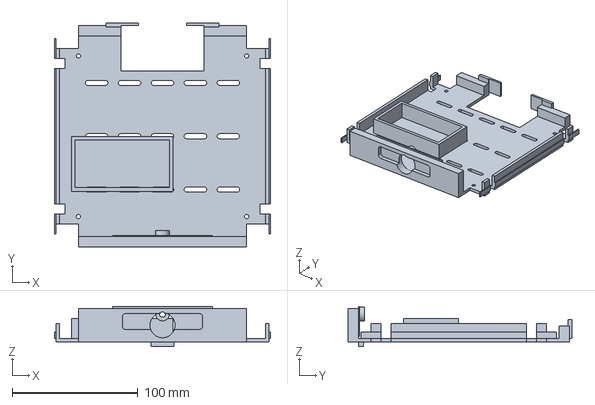
[picture p32: CAD file, 2026-06-27, last stored version]
revisions/mk0.7/review_package/exports/printable/plastic/external_ssd_bay.step
172.0 x 178.0 x 32.0 mm
