savchuk-sergey/homelab_modular_tower/revisions/mk0.7/review_package/exports/printable/plastic/left_foot_extension.step

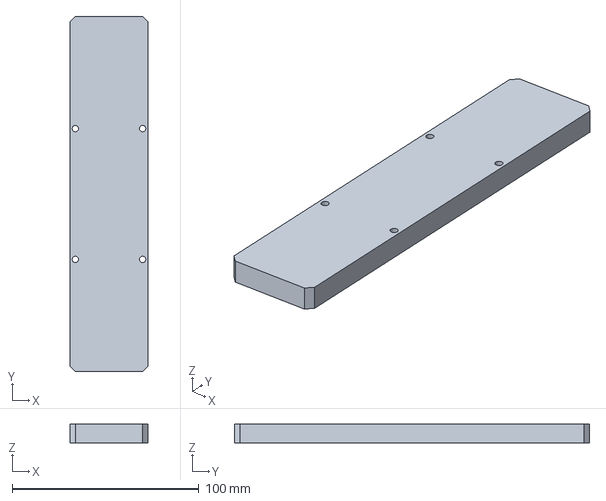
[picture p33: CAD file, 2026-06-27, last stored version]
revisions/mk0.7/review_package/exports/printable/plastic/left_foot_extension.step
42.0 x 190.0 x 10.0 mm
