savchuk-sergey/homelab_modular_tower/revisions/mk0.7/review_package/exports/printable/plastic/power_bus_cover.step

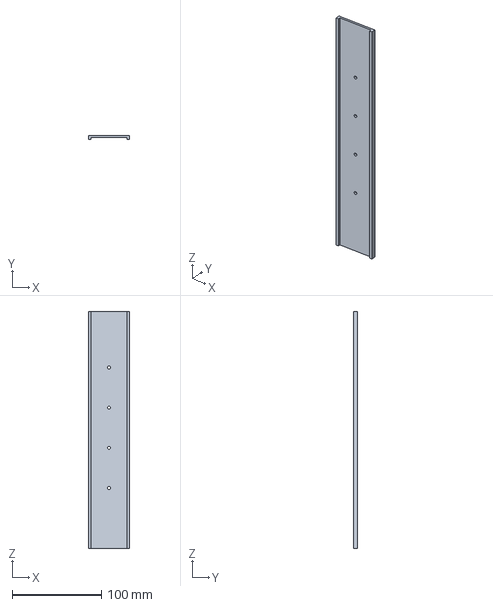
[picture p34: CAD file, 2026-06-27, last stored version]
revisions/mk0.7/review_package/exports/printable/plastic/power_bus_cover.step
46.0 x 5.00 x 265.5 mm
