savchuk-sergey/homelab_modular_tower/revisions/mk0.7/review_package/exports/printable/plastic/rear_service_spine.step

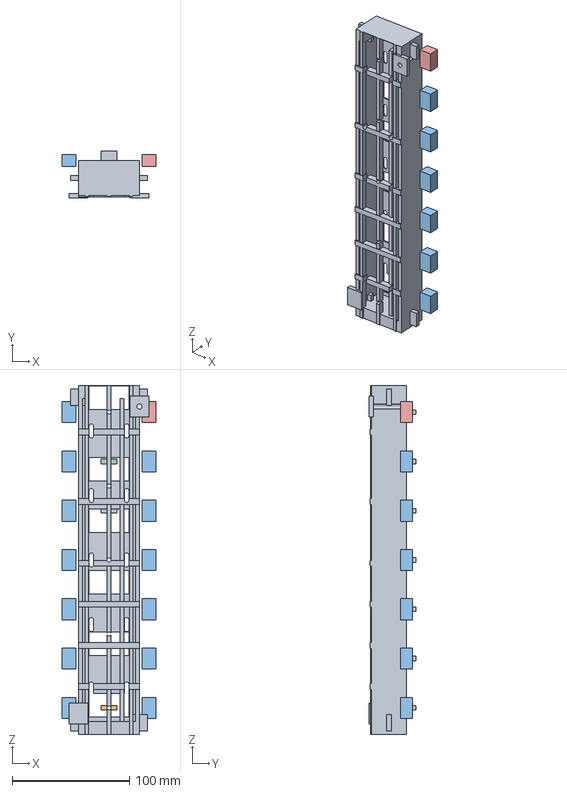
[picture p35: CAD file, 2026-06-27, last stored version]
revisions/mk0.7/review_package/exports/printable/plastic/rear_service_spine.step
80.0 x 40.0 x 297.5 mm
