savchuk-sergey/homelab_modular_tower/revisions/mk0.7/review_package/exports/printable/plastic/mini_pc_airflow_duct.step

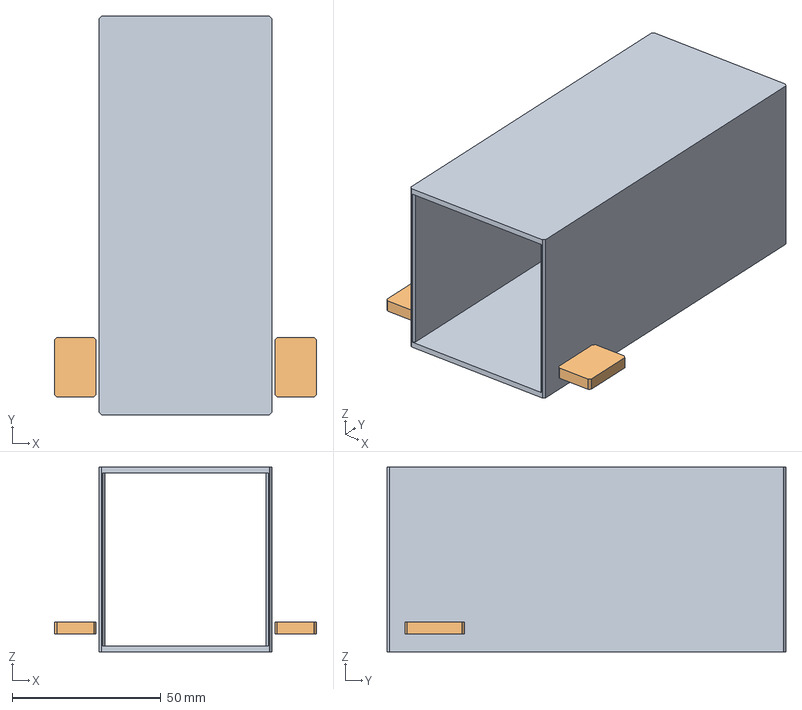
[picture p36: CAD file, 2026-06-27, last stored version]
revisions/mk0.7/review_package/exports/printable/plastic/mini_pc_airflow_duct.step
88.0 x 134.0 x 62.0 mm
