savchuk-sergey/homelab_modular_tower/revisions/mk0.7/review_package/exports/printable/plastic/bottom_fan_cartridge.step

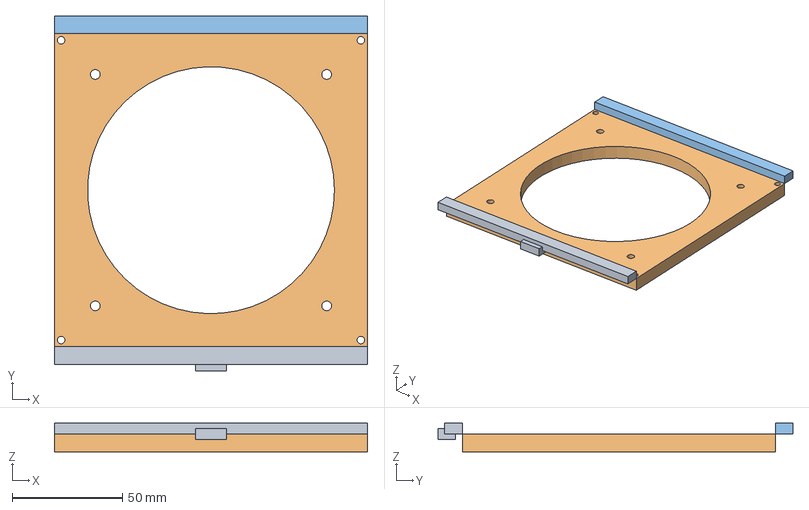
[picture p37: CAD file, 2026-06-27, last stored version]
revisions/mk0.7/review_package/exports/printable/plastic/bottom_fan_cartridge.step
142.0 x 161.0 x 13.0 mm
