savchuk-sergey/homelab_modular_tower/revisions/mk0.7/review_package/exports/printable/plastic/right_side_panel_upper.step

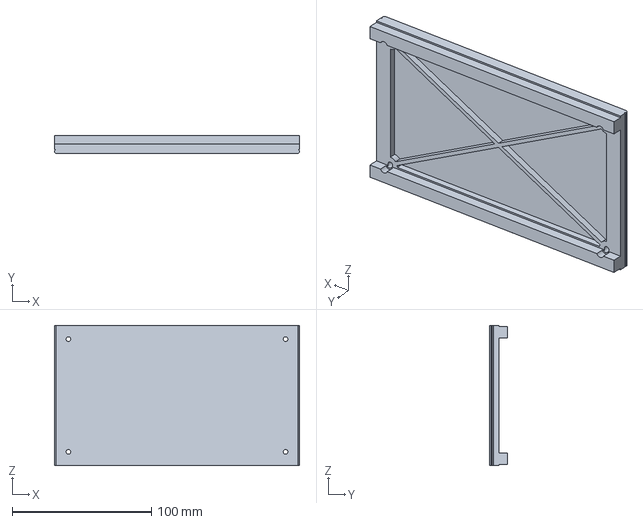
[picture p38: CAD file, 2026-06-27, last stored version]
revisions/mk0.7/review_package/exports/printable/plastic/right_side_panel_upper.step
176.0 x 13.0 x 100.9 mm
