savchuk-sergey/homelab_modular_tower/revisions/mk0.7/review_package/exports/printable/plastic/right_side_panel_middle.step

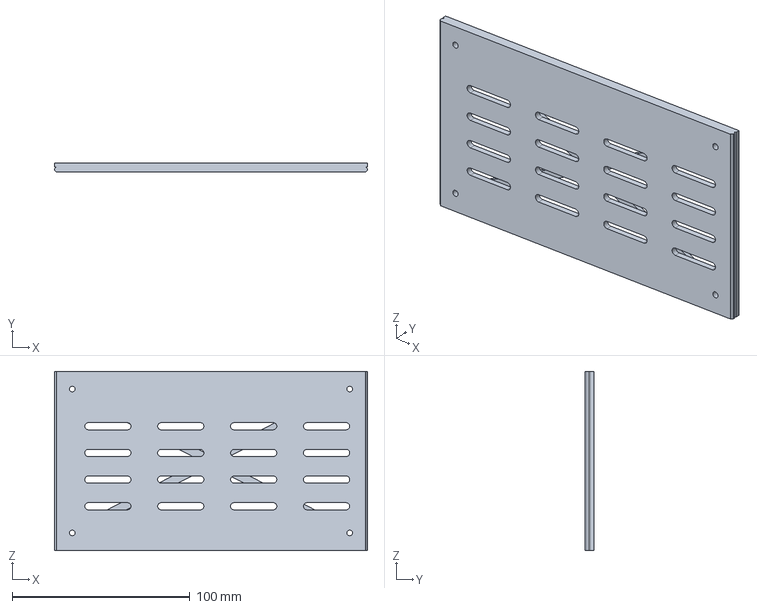
[picture p39: CAD file, 2026-06-27, last stored version]
revisions/mk0.7/review_package/exports/printable/plastic/right_side_panel_middle.step
176.0 x 5.20 x 100.9 mm
