savchuk-sergey/homelab_modular_tower/revisions/mk0.7/review_package/exports/printable/plastic/bottom_filter_retainer.step

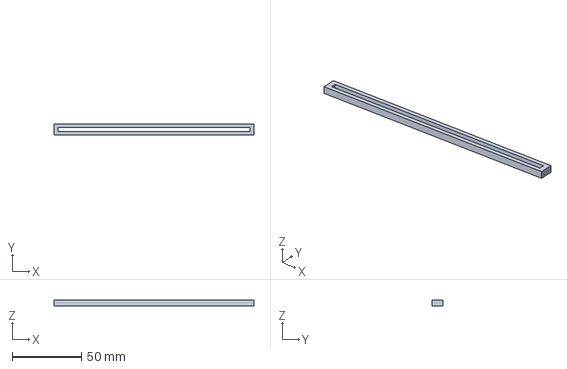
[picture p40: CAD file, 2026-06-27, last stored version]
revisions/mk0.7/review_package/exports/printable/plastic/bottom_filter_retainer.step
144.0 x 8.00 x 4.00 mm
