savchuk-sergey/homelab_modular_tower/revisions/mk0.7/review_package/exports/printable/plastic/bottom_fan_grille.step

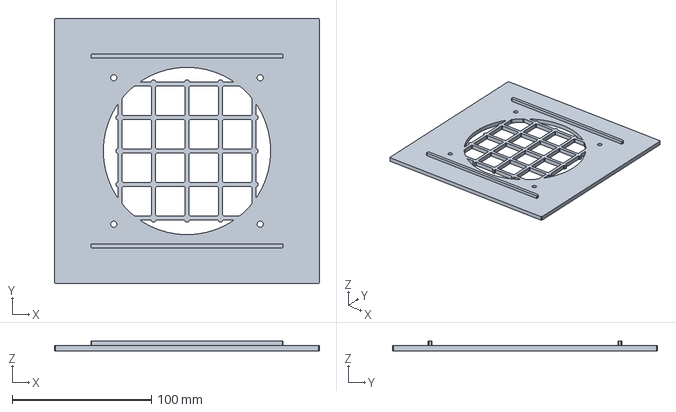
[picture p41: CAD file, 2026-06-27, last stored version]
revisions/mk0.7/review_package/exports/printable/plastic/bottom_fan_grille.step
190.0 x 190.0 x 7.00 mm
