savchuk-sergey/homelab_modular_tower/revisions/mk0.7/review_package/exports/printable/plastic/mini_pc_tray_stop.step

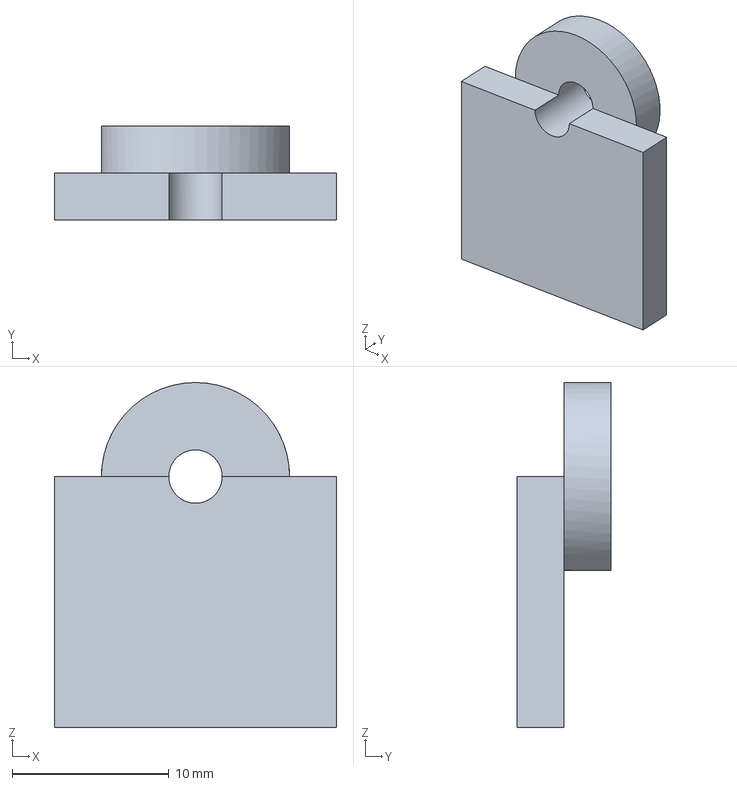
[picture p42: CAD file, 2026-06-27, last stored version]
revisions/mk0.7/review_package/exports/printable/plastic/mini_pc_tray_stop.step
18.0 x 6.00 x 22.0 mm
