savchuk-sergey/homelab_modular_tower/revisions/mk0.7/review_package/exports/printable/plastic/foot.step

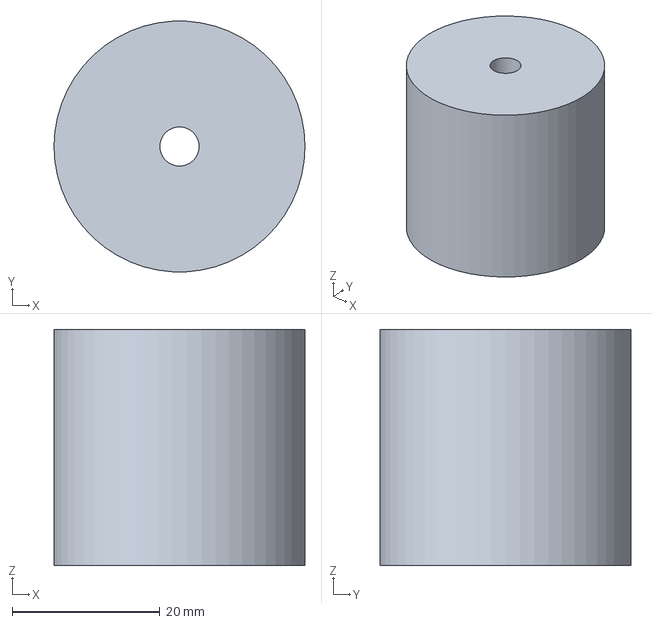
[picture p43: CAD file, 2026-06-27, last stored version]
revisions/mk0.7/review_package/exports/printable/plastic/foot.step
34.0 x 33.9 x 32.0 mm
