savchuk-sergey/homelab_modular_tower/revisions/mk0.7/review_package/exports/printable/plastic/power_bus_panel.step

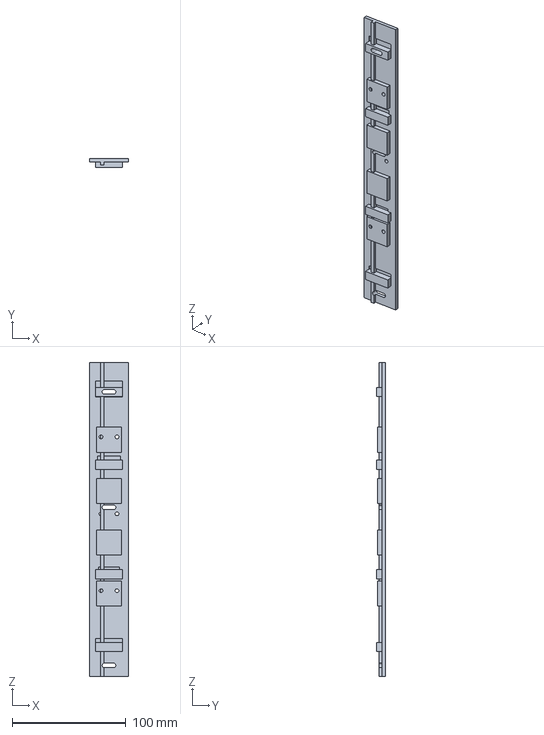
[picture p45: CAD file, 2026-06-27, last stored version]
revisions/mk0.7/review_package/exports/printable/plastic/power_bus_panel.step
34.0 x 7.50 x 275.5 mm
