savchuk-sergey/homelab_modular_tower/revisions/mk0.9.3/review_package/ASSEMBLY_OVERVIEW.md

# mk0.9.3 Assembly Overview

This file summarizes available generated artifacts for external review. It does not validate fit, strength, airflow, print orientation, or assembly procedure.

- printable STL: `0`
- non-printable STL: `0`
- placeholder STL: `0`
- review STL: `5`
- assembly STEP: `1`

Primary assembly artifact:

- `revisions/mk0.9.3/review_package/exports/assemblies/assembly.step`
