savchuk-sergey/homelab_modular_tower/revisions/mk0.7.4/REVIEW_GEOMETRY.md

# Review Geometry

Revision: `mk0.7.4`

This manifest lists generated export artifacts. CadQuery source remains the source of truth.

## airflow_path_review

- Category: `review`
- STEP: `exports/mk0.7.4/review/airflow_path_review.step`
- STL: `exports/mk0.7.4/review/airflow_path_review.stl`

## blocked_air_zones_review

- Category: `review`
- STEP: `exports/mk0.7.4/review/blocked_air_zones_review.step`
- STL: `exports/mk0.7.4/review/blocked_air_zones_review.stl`

## bottom_intake_open_area_review

- Category: `review`
- STEP: `exports/mk0.7.4/review/bottom_intake_open_area_review.step`
- STL: `exports/mk0.7.4/review/bottom_intake_open_area_review.stl`

## mini_pc_airflow_path_review

- Category: `review`
- STEP: `exports/mk0.7.4/review/mini_pc_airflow_path_review.step`
- STL: `exports/mk0.7.4/review/mini_pc_airflow_path_review.stl`

## power_bus_cover_reference

- Category: `review`
- STEP: `exports/mk0.7.4/review/power_bus_cover_reference.step`
- STL: `exports/mk0.7.4/review/power_bus_cover_reference.stl`

## power_bus_panel_reference

- Category: `review`
- STEP: `exports/mk0.7.4/review/power_bus_panel_reference.step`
- STL: `exports/mk0.7.4/review/power_bus_panel_reference.stl`

## printability_layout_review

- Category: `review`
- STEP: `exports/mk0.7.4/review/printability_layout_review.step`
- STL: `exports/mk0.7.4/review/printability_layout_review.stl`

## rear_service_spine_cover_reference

- Category: `review`
- STEP: `exports/mk0.7.4/review/rear_service_spine_cover_reference.step`
- STL: `exports/mk0.7.4/review/rear_service_spine_cover_reference.stl`

## rear_service_spine_reference

- Category: `review`
- STEP: `exports/mk0.7.4/review/rear_service_spine_reference.step`
- STL: `exports/mk0.7.4/review/rear_service_spine_reference.stl`

## stability_review

- Category: `review`
- STEP: `exports/mk0.7.4/review/stability_review.step`
- STL: `exports/mk0.7.4/review/stability_review.stl`
