savchuk-sergey/homelab_modular_tower/revisions/mk0.6/ENGINEERING_NOTES.md

# mk0.6 Engineering Notes

## Rear Spine как силовой элемент

В mk0.5 rear service spine был близок к кабельному каналу. В mk0.6 он получил отдельную силовую роль: вертикальные backbone ribs, горизонтальные перемычки на уровнях модулей, mounting tabs к верхней/нижней зоне и боковые ears рядом с задним силовым контуром. Съемная крышка остается сервисной деталью и не считается главным structural member.

## Сопротивление скручиванию

Основной load path mk0.6: M5 threaded rods, top/bottom structural frames, reinforced corner blocks, sectional side shear panels и rear service spine. Rear spine замыкает заднюю грань башни и снижает зависимость от пластиковых tray-модулей. Side panels работают как съемные shear cassettes, а не как декоративные накладки.

Компромисс: съемные панели и крышки уступают цельной коробчатой раме по жесткости, но сохраняют ремонтопригодность и доступ к модулям.

## База устойчивости

База разделена на центральный fan frame, две боковые extensions и два stability wings. Это сохраняет увеличенный footprint, но убирает необходимость печатать одну большую PETG-плиту. TPU feet увеличены до `25 mm`, чтобы нижний intake имел рабочий зазор от стола.

Компромисс: секционная база требует больше винтов и сборочных операций, зато печатается проще и легче заменяется по частям.

## Tray-модули

Все trays проходят через общий standard interface. Общая геометрия включает одинаковую ширину посадки, front handle, front lock, rear stop, cable exit, rail features и mounting holes. Device-specific код добавляет только локальные placeholder zones, pockets или windows, не меняя базовый модульный стандарт.

Компромисс: общий стандарт ограничивает свободу отдельных модулей, но снижает риск несовместимых tray-ревизий.

## Power Bus

Power bus расположен в rear service spine и остается только DC-зоной. В mk0.6 добавлены защитная крышка, strain relief, signal/power divider, connector windows и cable-tie slots. Маркировочные зоны заданы через `POWER_BUS_RAIL_LABELS` для `19V`, `12V`, `5V`, `GND`.

Компромисс: footprints пока обобщенные, потому что точные terminal/fuse/DC-DC компоненты еще не выбраны.

## Airflow

Схема остается вертикальной: 120 mm bottom intake и 120 mm top exhaust. Mini PC получает отдельный duct placeholder и review path. Rear spine не должен перекрывать центральный вертикальный поток, а cable routing уводится назад. Добавлены sensor mounting markers для будущего размещения температурных датчиков.

Компромисс: review arrows и blocked zones являются инженерной визуализацией, а не CFD.

## Принятые инженерные компромиссы

- Секционная база сложнее в сборке, но лучше для PETG-печати и ремонта.
- Rear spine усилен, но не превращен в несъемную заднюю стенку, чтобы сохранить сервисный доступ.
- Power bus получил защиту и routing intent, но точная электрическая механика оставлена на этап выбора компонентов.
- Tray standard унифицирован, хотя отдельным устройствам позже могут потребоваться адаптеры.
- Review geometry добавлена как отдельные детали, чтобы не смешивать production geometry и проверочные визуализации.
