savchuk-sergey/homelab_modular_tower/revisions/mk0.7/review_package/exports/MANIFEST.md

# mk0.7 export manifest

Generated from CadQuery source. STEP/STL files are derived artifacts.

## printable/plastic

- `bottom_fan_cartridge`
- `bottom_fan_grille`
- `bottom_filter_frame`
- `bottom_filter_retainer`
- `bottom_structural_frame`
- `central_bottom_fan_frame`
- `corner_block`
- `external_ssd_bay`
- `foot`
- `foot_socket`
- `frame_bottom`
- `frame_top`
- `front_stability_wing`
- `left_foot_extension`
- `left_side_panel_lower`
- `left_side_panel_middle`
- `left_side_panel_upper`
- `mikrotik_tray`
- `mini_pc_airflow_duct`
- `mini_pc_tray`
- `mini_pc_tray_stop`
- `power_bus_cover`
- `power_bus_panel`
- `raspberry_pi_tray`
- `rear_service_spine`
- `rear_service_spine_cover`
- `rear_stability_wing`
- `right_foot_extension`
- `right_side_panel_lower`
- `right_side_panel_middle`
- `right_side_panel_upper`
- `ssd_expansion_tray`
- `top_fan_grille`
- `top_structural_frame`
- `ups_power_tray`

## non_printable/metal_reference

- `m5_threaded_rod`
- `metal_guide_rail`

## placeholders/devices

- `mikrotik_placeholder`
- `mini_pc_placeholder`
- `raspberry_pi_3b_placeholder`
- `ssd_expansion_placeholder`
- `ssd_placeholder`
- `ups_placeholder`

## placeholders/fans

- `fan_120x120x25_placeholder`

## review

- `airflow_path_review`
- `blocked_air_zones_review`
- `bottom_intake_open_area_review`
- `mini_pc_airflow_path_review`
- `printability_layout_review`
- `stability_review`
