savchuk-sergey/homelab_modular_tower/revisions/mk0.9/PLACEHOLDERS.md

# Device and Fan Placeholders

Revision: `mk0.9`

This manifest lists generated export artifacts. CadQuery source remains the source of truth.

## external_ssd_placeholder

- Category: `placeholders`
- STEP: `exports/mk0.9/placeholders/devices/external_ssd_placeholder.step`
- STL: `exports/mk0.9/placeholders/devices/external_ssd_placeholder.stl`

## mini_pc_placeholder

- Category: `placeholders`
- STEP: `exports/mk0.9/placeholders/devices/mini_pc_placeholder.step`
- STL: `exports/mk0.9/placeholders/devices/mini_pc_placeholder.stl`

## raspberry_pi_3b_placeholder

- Category: `placeholders`
- STEP: `exports/mk0.9/placeholders/devices/raspberry_pi_3b_placeholder.step`
- STL: `exports/mk0.9/placeholders/devices/raspberry_pi_3b_placeholder.stl`

## fan_120x120x25_placeholder

- Category: `placeholders`
- STEP: `exports/mk0.9/placeholders/fans/fan_120x120x25_placeholder.step`
- STL: `exports/mk0.9/placeholders/fans/fan_120x120x25_placeholder.stl`

## dust_filter_placeholder

- Category: `placeholders`
- STEP: `exports/mk0.9/placeholders/filters/dust_filter_placeholder.step`
- STL: `exports/mk0.9/placeholders/filters/dust_filter_placeholder.stl`

## top_guard_filter_mesh_placeholder

- Category: `placeholders`
- STEP: `exports/mk0.9/placeholders/filters/top_guard_filter_mesh_placeholder.step`
- STL: `exports/mk0.9/placeholders/filters/top_guard_filter_mesh_placeholder.stl`
