savchuk-sergey/homelab_modular_tower/revisions/mk0.9/REVIEW_GEOMETRY.md

# Review Geometry

Revision: `mk0.9`

This manifest lists generated export artifacts. CadQuery source remains the source of truth.

## airflow_clearance_zone

- Category: `review`
- STEP: `exports/mk0.9/review/airflow_clearance_zone.step`
- STL: `exports/mk0.9/review/airflow_clearance_zone.stl`

## central_airflow_channel_placeholder

- Category: `review`
- STEP: `exports/mk0.9/review/central_airflow_channel_placeholder.step`
- STL: `exports/mk0.9/review/central_airflow_channel_placeholder.stl`

## module_interface_bottom

- Category: `review`
- STEP: `exports/mk0.9/review/module_interface_bottom.step`
- STL: `exports/mk0.9/review/module_interface_bottom.stl`

## module_interface_top

- Category: `review`
- STEP: `exports/mk0.9/review/module_interface_top.step`
- STL: `exports/mk0.9/review/module_interface_top.stl`

## simplified_airflow_guide

- Category: `review`
- STEP: `exports/mk0.9/review/simplified_airflow_guide.step`
- STL: `exports/mk0.9/review/simplified_airflow_guide.stl`
