savchuk-sergey/homelab_modular_tower/revisions/mk0.7.3/PLACEHOLDERS.md

# Device and Fan Placeholders

Revision: `mk0.7.3`

This manifest lists generated export artifacts. CadQuery source remains the source of truth.

## mikrotik_placeholder

- Category: `placeholders`
- STEP: `exports/mk0.7.3/placeholders/devices/mikrotik_placeholder.step`
- STL: `exports/mk0.7.3/placeholders/devices/mikrotik_placeholder.stl`

## mini_pc_placeholder

- Category: `placeholders`
- STEP: `exports/mk0.7.3/placeholders/devices/mini_pc_placeholder.step`
- STL: `exports/mk0.7.3/placeholders/devices/mini_pc_placeholder.stl`

## power_bus_zone_placeholder

- Category: `placeholders`
- STEP: `exports/mk0.7.3/placeholders/devices/power_bus_zone_placeholder.step`
- STL: `exports/mk0.7.3/placeholders/devices/power_bus_zone_placeholder.stl`

## raspberry_pi_3b_placeholder

- Category: `placeholders`
- STEP: `exports/mk0.7.3/placeholders/devices/raspberry_pi_3b_placeholder.step`
- STL: `exports/mk0.7.3/placeholders/devices/raspberry_pi_3b_placeholder.stl`

## ssd_expansion_placeholder

- Category: `placeholders`
- STEP: `exports/mk0.7.3/placeholders/devices/ssd_expansion_placeholder.step`
- STL: `exports/mk0.7.3/placeholders/devices/ssd_expansion_placeholder.stl`

## ssd_placeholder

- Category: `placeholders`
- STEP: `exports/mk0.7.3/placeholders/devices/ssd_placeholder.step`
- STL: `exports/mk0.7.3/placeholders/devices/ssd_placeholder.stl`

## ups_placeholder

- Category: `placeholders`
- STEP: `exports/mk0.7.3/placeholders/devices/ups_placeholder.step`
- STL: `exports/mk0.7.3/placeholders/devices/ups_placeholder.stl`

## fan_120x120x25_placeholder

- Category: `placeholders`
- STEP: `exports/mk0.7.3/placeholders/fans/fan_120x120x25_placeholder.step`
- STL: `exports/mk0.7.3/placeholders/fans/fan_120x120x25_placeholder.stl`
