savchuk-sergey/homelab_modular_tower/revisions/mk0.7/review_package/manifests/REVIEW_GEOMETRY.md

# Review Geometry

Revision: `mk0.7`

This manifest lists generated export artifacts. CadQuery source remains the source of truth.

## airflow_path_review

- Category: `review`
- STEP: `exports/mk0.7/review/airflow_path_review.step`
- STL: `exports/mk0.7/review/airflow_path_review.stl`

## blocked_air_zones_review

- Category: `review`
- STEP: `exports/mk0.7/review/blocked_air_zones_review.step`
- STL: `exports/mk0.7/review/blocked_air_zones_review.stl`

## bottom_intake_open_area_review

- Category: `review`
- STEP: `exports/mk0.7/review/bottom_intake_open_area_review.step`
- STL: `exports/mk0.7/review/bottom_intake_open_area_review.stl`

## mini_pc_airflow_path_review

- Category: `review`
- STEP: `exports/mk0.7/review/mini_pc_airflow_path_review.step`
- STL: `exports/mk0.7/review/mini_pc_airflow_path_review.stl`

## printability_layout_review

- Category: `review`
- STEP: `exports/mk0.7/review/printability_layout_review.step`
- STL: `exports/mk0.7/review/printability_layout_review.stl`

## stability_review

- Category: `review`
- STEP: `exports/mk0.7/review/stability_review.step`
- STL: `exports/mk0.7/review/stability_review.stl`
