savchuk-sergey/homelab_modular_tower/revisions/mk0.5/REVISION.md

# mk0.5 - Stability and Torsional Stiffness Revision

## 1. Цель ревизии

mk0.5 развивает стабильную mk0.4 без полной переработки корпуса. Ревизия решает две инженерные проблемы:

- риск опрокидывания высокой башни около 360 мм;
- недоказанную крутильную жесткость силового контура.

## 2. Что изменено

- Добавлено расширенное основание `base_stability_plate`.
- Ножки вынесены к углам расширенного footprint.
- TPU-ножка отделена от PETG-посадочного гнезда.
- Rear Service Spine усилена как вертикальный силовой элемент.
- Нижние и верхние боковые секции работают как shear panels.
- Mini PC tray получил винтовой ограничитель сервисного выдвижения.
- Добавлены точки под будущий torsion brace kit.
- Добавлены review render targets для stability, torsion и mini PC service position.

## 3. Что НЕ изменялось намеренно

- Порядок модулей.
- Модульная сетка.
- Общая архитектура Mini Blade Tower.
- Power bus как полноценная электрическая система.
- Полный airflow-дизайн.
- Габариты всех модулей.

mk0.5 не решает полностью airflow и не решает полностью power bus. Это не финальная эксплуатационная версия.

## 4. Новые детали

- `make_base_stability_plate()`
- `make_foot_socket()`
- `make_wide_tpu_foot_placeholder()`
- `make_tray_stop()`

## 5. Изменённые детали

- `create_rear_service_spine()`
- `create_rear_service_spine_cover()`
- `make_side_panel_tile()`
- `create_mini_pc_tray()`
- `build_assembly()`

## 6. Инженерная логика

Устойчивость улучшена не увеличением всего корпуса, а расширением нижнего опорного контура. Крутильная жесткость улучшена замыканием силового пути: нижняя рама, верхняя рама, M5-шпильки, rear spine и прикрученные боковые shear panels работают вместе.

## 7. Влияние на прочность

Положительное: база и rear spine добавляют силовой путь, а боковые панели уменьшают ромбование. Ограничение: PETG-панели не заменяют металлические диагонали, поэтому torsion brace kit оставлен как future upgrade.

## 8. Влияние на устойчивость

Положительное: footprint основания больше footprint корпуса, а ножки вынесены ближе к углам. Mini PC tray stop снижает риск полного случайного выдвижения тяжелого верхнего модуля.

## 9. Влияние на печать

Основание остается отдельной плоской PETG-деталью с ребрами вместо массивной плиты. TPU-ножки печатаются отдельно. Боковые панели остаются секционными.

## 10. Влияние на сборку

Сборка усложняется умеренно: появляются винтовые точки rear spine cover, shear panels и tray stop. Взамен сервисные детали остаются съемными.

## 11. Влияние на обслуживание

Положительное: модули остаются съемными, rear service spine сохраняет кабельный канал, а foot/stop элементы заменяемы. Полное снятие mini PC tray требует осознанного действия.

## 12. Компромиссы

- База увеличивает площадь на столе.
- Дополнительные винты увеличивают время сборки.
- Усиленный spine может потребовать проверки печати длинной детали или секционирования в mk0.6+.
- Shear panels повышают жесткость, но требуют аккуратного затягивания винтов.

## 13. Что проверить физическим тестом

Перед полной печатью желательно напечатать test-rig:

1. Башня не должна легко качаться вперед-назад.
2. При выдвижении mini PC tray задние ножки не должны отрываться от стола.
3. Корпус не должен легко скручиваться руками.
4. Rear spine не должна люфтить.
5. Боковая shear panel не должна трещать в креплениях.
6. Должен сохраняться доступ к винтам.
7. Нижний airflow не должен быть перекрыт основанием.

## 14. Риски, оставшиеся на mk0.6+

- Реальная жесткость зависит от материала, infill, ориентации печати и качества heat-set inserts.
- Нужна физическая проверка длинной rear spine.
- Нужен airflow-тест с реальным mini PC.
- Нужны реальные размеры power bus компонентов и разъемов.
- Torsion brace kit пока подготовлен точками крепления, но не валидирован как обязательная часть конструкции.
