savchuk-sergey/homelab_modular_tower/cad/parts/airflow.py

"""Backward-compatibility stub — file moved to cad/legacy/parts/airflow.py."""
from cad.legacy.parts.airflow import *  # noqa: F401, F403
from cad.legacy.parts.airflow import (
    make_airflow_clearance_zone,
    make_central_airflow_channel_placeholder,
    make_simplified_airflow_guide,
)
