savchuk-sergey/homelab_modular_tower/cad/parts/base_module.py

"""Backward-compatibility stub — file moved to cad/legacy/parts/base_module.py."""
from cad.legacy.parts.base_module import (  # noqa: F401
    make_base_fan_mount,
    make_base_frame,
    make_base_module,
    make_bottom_grill,
    make_dust_filter_slot,
    make_foot_mounts,
)
