savchuk-sergey/homelab_modular_tower/cad/parts/cooling.py

"""Backward-compatibility stub — file moved to cad/legacy/parts/cooling.py."""
from cad.legacy.parts.cooling import (  # noqa: F401
    create_bottom_fan_cartridge,
    create_bottom_fan_panel,
    create_bottom_filter_frame,
    create_bottom_filter_retainer,
    create_fan_panel,
    create_mini_pc_airflow_duct,
    create_top_fan_panel,
    make_bottom_fan_cartridge,
    make_bottom_fan_grille,
    make_bottom_filter_frame,
    make_bottom_filter_retainer,
    make_fan_grille,
    make_mini_pc_airflow_duct_placeholder,
    make_top_fan_grille,
)
