savchuk-sergey/homelab_modular_tower/cad/parts/corner_blocks.py

"""Backward-compatibility stub — file moved to cad/legacy/parts/corner_blocks.py."""
from cad.legacy.parts.corner_blocks import (  # noqa: F401
    create_corner_block,
    create_corner_blocks_in_place,
)
