savchuk-sergey/homelab_modular_tower/cad/parts/frame.py

"""Backward-compatibility stub — file moved to cad/legacy/parts/frame.py."""
from cad.legacy.parts.frame import (  # noqa: F401
    create_frame_bottom,
    create_frame_ring,
    create_frame_top,
    make_bottom_structural_frame,
    make_top_structural_frame,
)
