savchuk-sergey/homelab_modular_tower/cad/parts/mini_pc_placeholder_module.py

"""Backward-compatibility stub — file moved to cad/legacy/parts/mini_pc_placeholder_module.py."""
from cad.legacy.parts.mini_pc_placeholder_module import (  # noqa: F401
    make_mini_pc_placeholder,
    make_mini_pc_placeholder_airflow_guide,
    make_mini_pc_placeholder_module,
    make_mini_pc_placeholder_module_shell,
    make_mini_pc_placeholder_retainer,
    make_mini_pc_placeholder_tray,
)
