savchuk-sergey/homelab_modular_tower/cad/parts/modules.py

"""Backward-compatibility stub — file moved to cad/legacy/parts/modules.py."""
from cad.legacy.parts.modules import (  # noqa: F401
    TRAY_FACTORIES,
    create_external_ssd_bay,
    create_mikrotik_tray,
    create_mini_pc_tray,
    create_raspberry_pi_tray,
    create_ssd_expansion_tray,
    create_ups_power_tray,
    make_tray_stop,
)
