savchuk-sergey/homelab_modular_tower/cad/parts/review.py

"""Backward-compatibility stub — file moved to cad/legacy/parts/review.py."""
from cad.legacy.parts.review import (  # noqa: F401
    make_airflow_path_review,
    make_blocked_air_zones_review,
    make_bottom_intake_open_area_review,
    make_mini_pc_airflow_path_review,
    make_printability_layout_review,
    make_stability_review,
)
