savchuk-sergey/homelab_modular_tower/cad/parts/roof_module.py

"""Backward-compatibility stub — file moved to cad/legacy/parts/roof_module.py."""
from cad.legacy.parts.roof_module import (  # noqa: F401
    make_fan_shroud,
    make_roof_frame,
    make_roof_module,
    make_top_fan_mount,
    make_top_filter_slot,
    make_top_grill,
)
