savchuk-sergey/homelab_modular_tower/cad/parts/rpi_ssd_module.py

"""Backward-compatibility stub — file moved to cad/legacy/parts/rpi_ssd_module.py."""
from cad.legacy.parts.rpi_ssd_module import (  # noqa: F401
    make_external_ssd_placeholder,
    make_rpi3_placeholder,
    make_rpi_mount_posts,
    make_rpi_ssd_module,
    make_rpi_ssd_module_shell,
    make_rpi_ssd_tray,
    make_ssd_retainer,
)
