savchuk-sergey/homelab_modular_tower/cad/parts/service_spine.py

"""Backward-compatibility stub — file moved to cad/legacy/parts/service_spine.py."""
from cad.legacy.parts.service_spine import (  # noqa: F401
    create_power_bus_cover,
    create_power_bus_cover_lower,
    create_power_bus_cover_upper,
    create_power_bus_panel,
    create_power_bus_panel_lower,
    create_power_bus_panel_upper,
    create_rear_service_spine,
    create_rear_service_spine_cover,
    create_rear_service_spine_cover_lower,
    create_rear_service_spine_cover_upper,
    create_rear_service_spine_lower,
    create_rear_service_spine_upper,
)
